ftrias/vindormusic/apps/juce-gui/Knob/JKnobMan/Resource/Images/JKnobMan.png

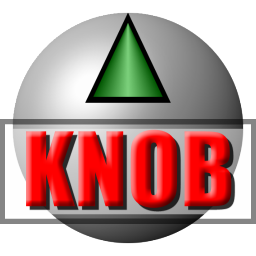
apps/juce-gui/Knob/JKnobMan/Resource/Images/JKnobMan.png
