ftrias/vindormusic/apps/juce-gui/Knob/JKnobMan/Texture/Plasma.bmp

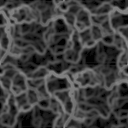
apps/juce-gui/Knob/JKnobMan/Texture/Plasma.bmp
