ftrias/vindormusic/apps/juce-gui/Assets/refresh.png

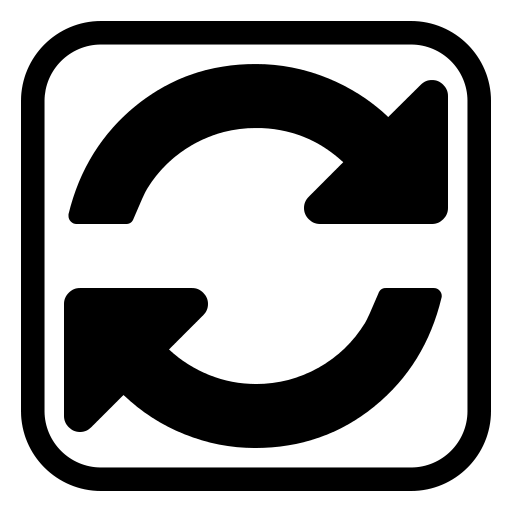
apps/juce-gui/Assets/refresh.png
