ftrias/vindormusic/apps/juce-gui/Assets/waveforms.png

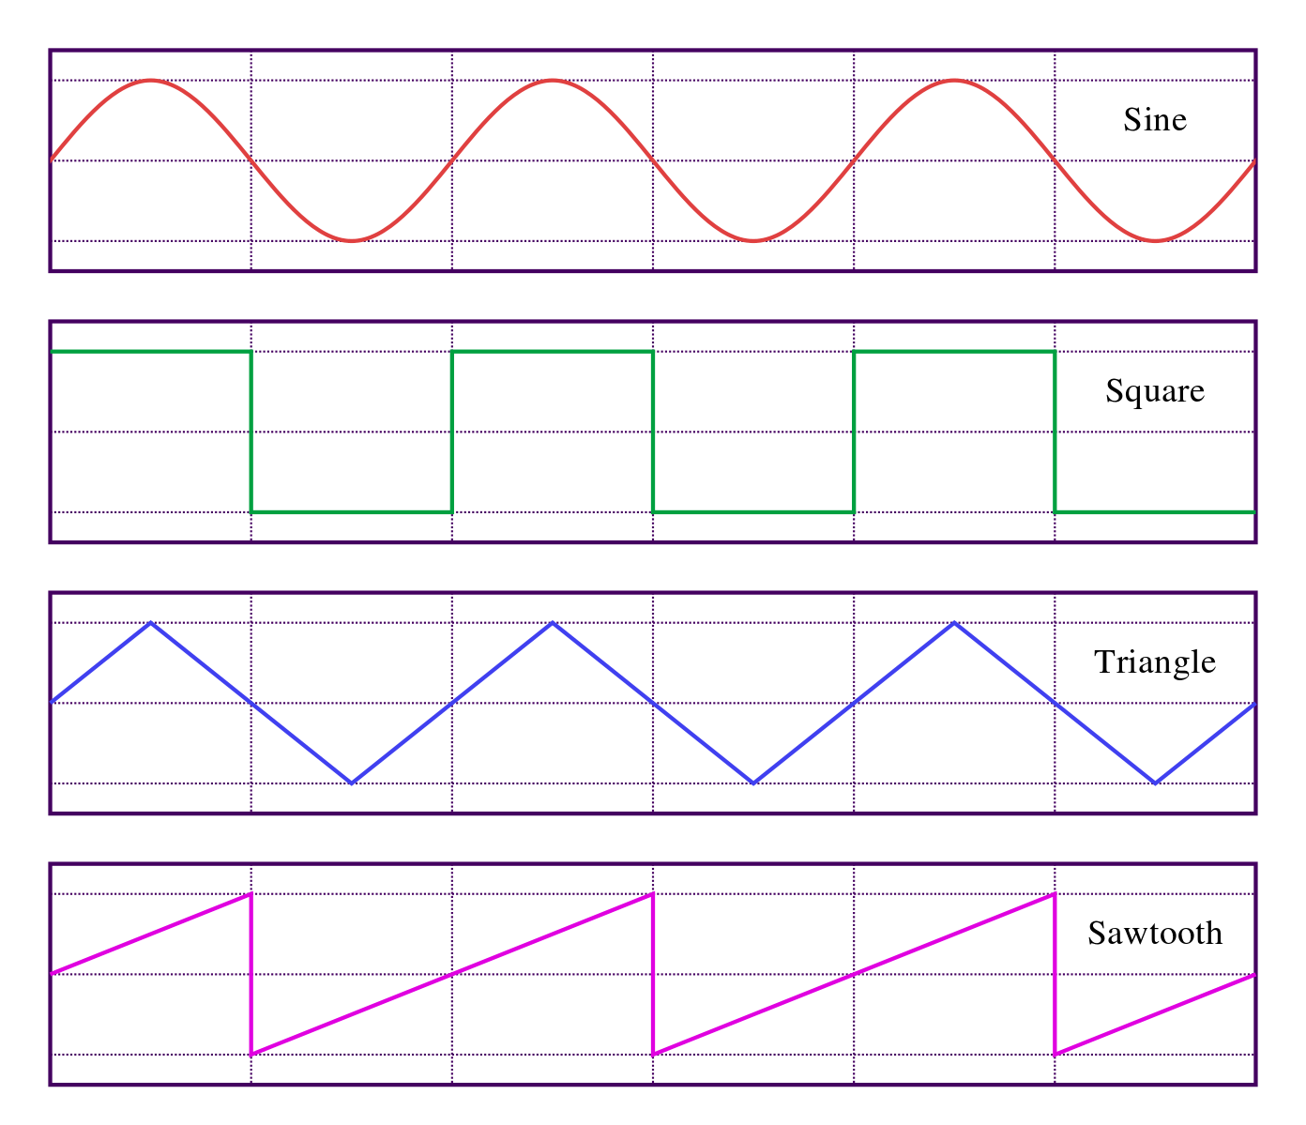
apps/juce-gui/Assets/waveforms.png
