ftrias/vindormusic/apps/juce-gui/Dist/Vindor WAP/Vindor WAP/Assets/LargeTile.scale-100.png

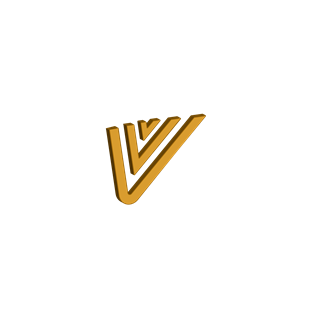
apps/juce-gui/Dist/Vindor WAP/Vindor WAP/Assets/LargeTile.scale-100.png
