ftrias/vindormusic/apps/juce-gui/Dist/Vindor WAP/Vindor WAP/Assets/SmallTile.scale-200.png

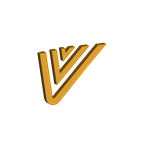
apps/juce-gui/Dist/Vindor WAP/Vindor WAP/Assets/SmallTile.scale-200.png
