ftrias/vindormusic/apps/juce-gui/Knob/JKnobMan/Resource/Images/pickercursor.png

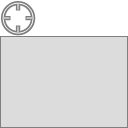
apps/juce-gui/Knob/JKnobMan/Resource/Images/pickercursor.png
