ftrias/vindormusic/apps/juce-gui/Knob/JKnobMan/Texture/Aura.jpg

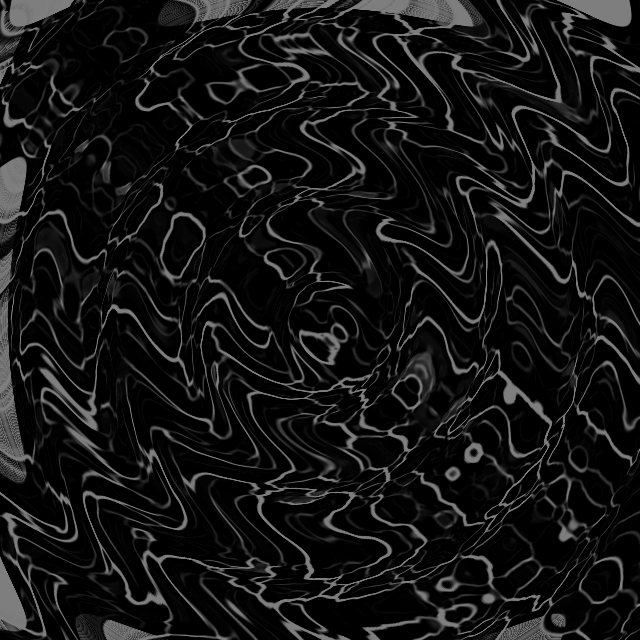
apps/juce-gui/Knob/JKnobMan/Texture/Aura.jpg
