ftrias/vindormusic/apps/juce-gui/Knob/JKnobMan/Texture/Circle.jpg

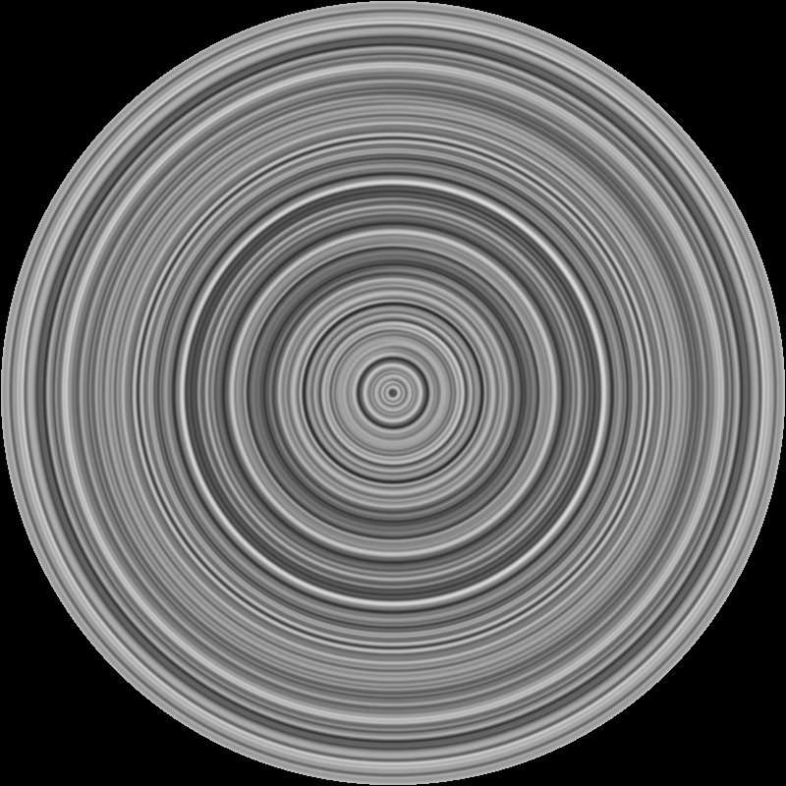
apps/juce-gui/Knob/JKnobMan/Texture/Circle.jpg
