ftrias/vindormusic/apps/juce-gui/Knob/JKnobMan/Texture/Coal.jpg

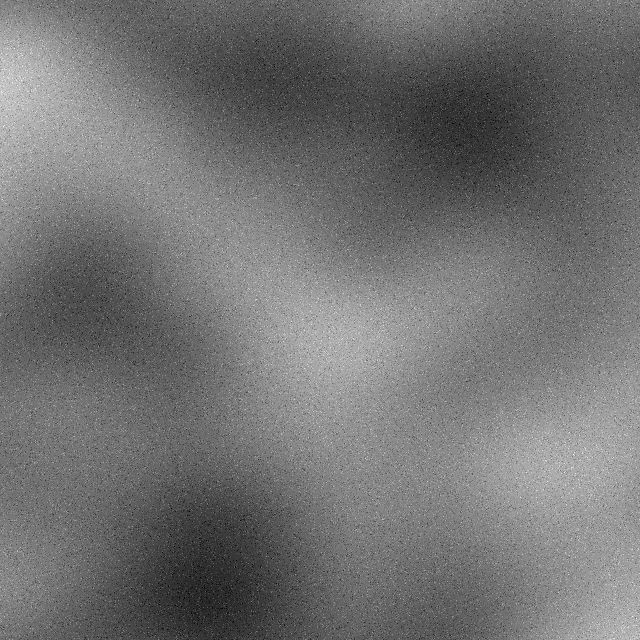
apps/juce-gui/Knob/JKnobMan/Texture/Coal.jpg
