ftrias/vindormusic/apps/juce-gui/Knob/JKnobMan/Texture/Fabric.bmp

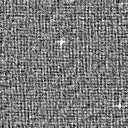
apps/juce-gui/Knob/JKnobMan/Texture/Fabric.bmp
