ftrias/vindormusic/apps/juce-gui/Knob/JKnobMan/Texture/Hairline.bmp

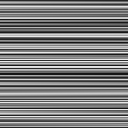
apps/juce-gui/Knob/JKnobMan/Texture/Hairline.bmp
