ftrias/vindormusic/apps/juce-gui/Knob/JKnobMan/Texture/HairlineV.bmp

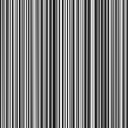
apps/juce-gui/Knob/JKnobMan/Texture/HairlineV.bmp
