ftrias/vindormusic/apps/juce-gui/Knob/JKnobMan/Texture/Magma.bmp

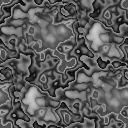
apps/juce-gui/Knob/JKnobMan/Texture/Magma.bmp
