ftrias/vindormusic/apps/juce-gui/Knob/JKnobMan/Texture/Mosaic.bmp

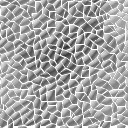
apps/juce-gui/Knob/JKnobMan/Texture/Mosaic.bmp
