ftrias/vindormusic/apps/juce-gui/Knob/JKnobMan/Texture/Plant.png

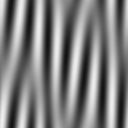
apps/juce-gui/Knob/JKnobMan/Texture/Plant.png
