ftrias/vindormusic/apps/juce-gui/Knob/JKnobMan/Texture/Radiation.jpg

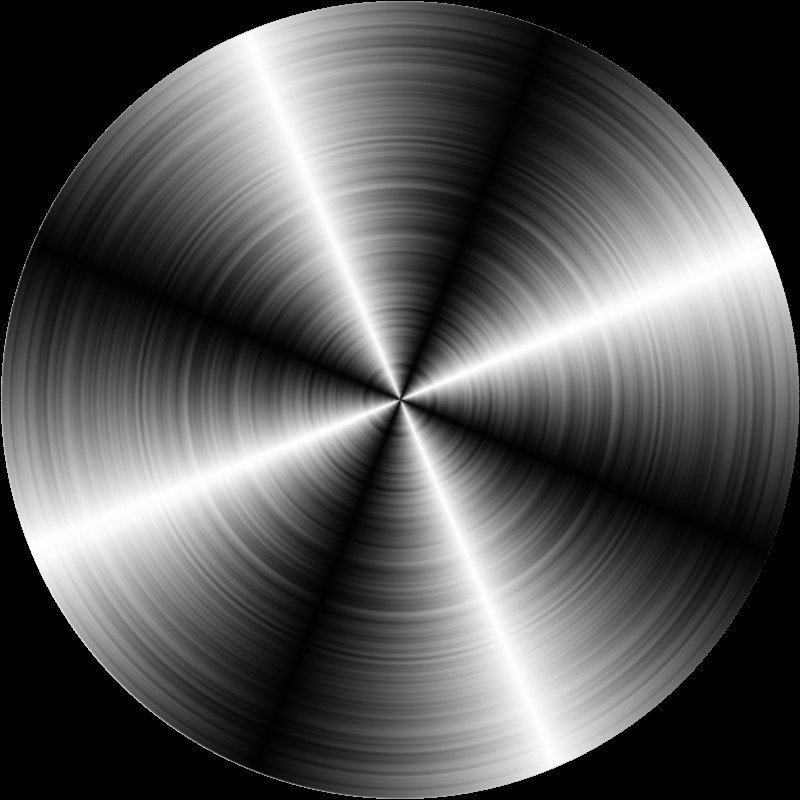
apps/juce-gui/Knob/JKnobMan/Texture/Radiation.jpg
