ftrias/vindormusic/apps/juce-gui/Knob/JKnobMan/Texture/Sand.bmp

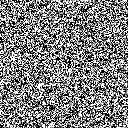
apps/juce-gui/Knob/JKnobMan/Texture/Sand.bmp
