ftrias/vindormusic/apps/juce-gui/Knob/JKnobMan/Texture/Scratch.jpg

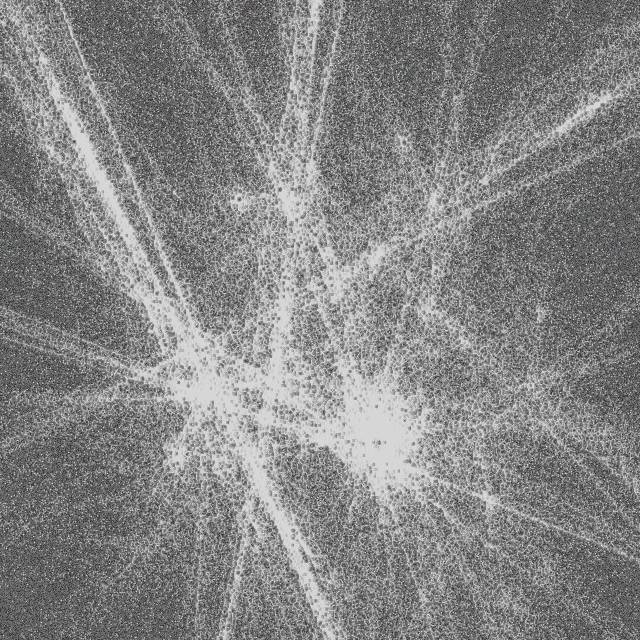
apps/juce-gui/Knob/JKnobMan/Texture/Scratch.jpg
