ftrias/vindormusic/apps/splayer/splayer/Source/Vindor.png

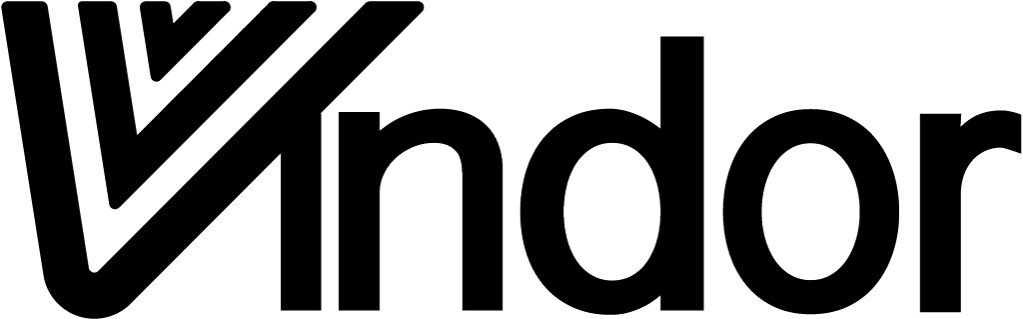
apps/splayer/splayer/Source/Vindor.png
