ftrias/vindormusic/shell/case/girl-playing.png

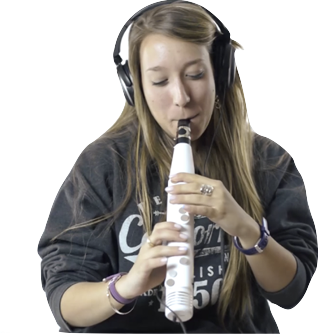
shell/case/girl-playing.png
