ftrias/vindormusic/shell/solidworks/Vindor RevD/2-56 screw 3_4in long 92196A084.SLDPRT

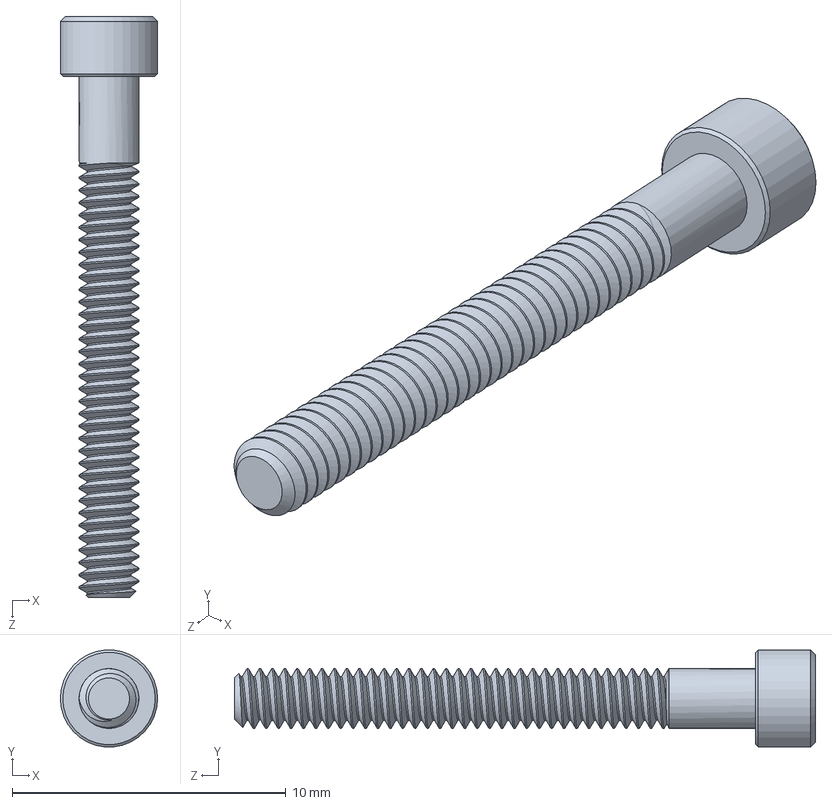
[picture p98: CAD file, 2024-02-22]
shell/solidworks/Vindor RevD/2-56 screw 3_4in long 92196A084.SLDPRT
3.56 x 3.54 x 21.2 mm
