ftrias/vindormusic/shell/solidworks/Vindor RevD/4-40 screw 7_16inlong 91772A109.SLDPRT

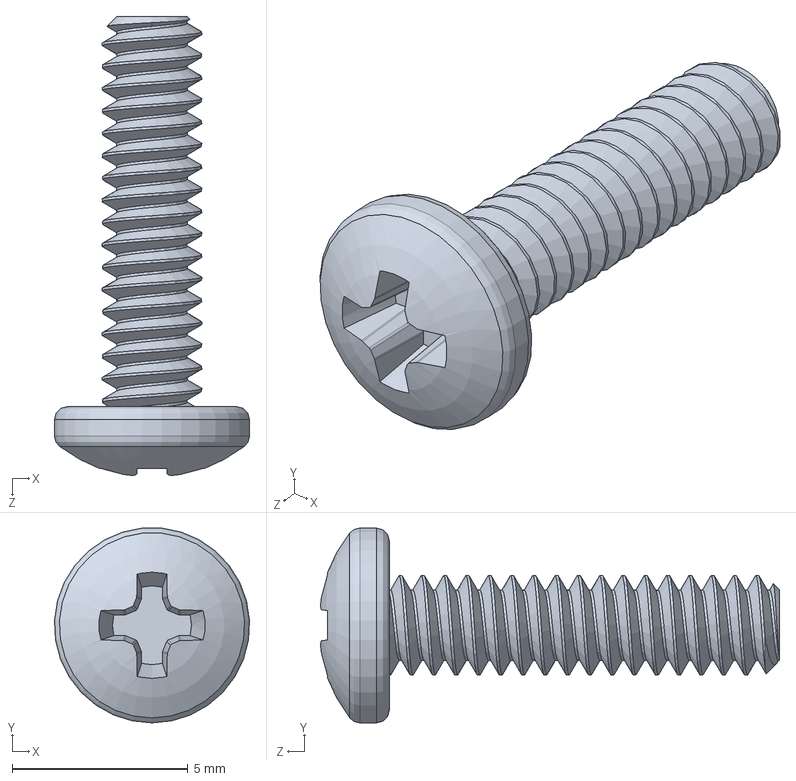
[picture p99: CAD file, 2024-02-22]
shell/solidworks/Vindor RevD/4-40 screw 7_16inlong 91772A109.SLDPRT
5.56 x 5.55 x 13.1 mm
