ftrias/vindormusic/shell/solidworks/Vindor RevD/4-40 Thread lock screw 1_4inlong 93802A421.SLDPRT

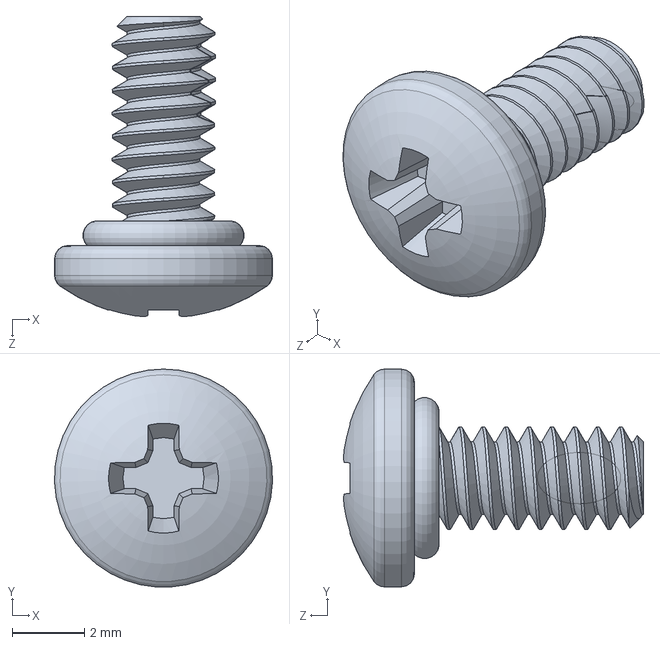
[picture p100: CAD file, 2024-02-22]
shell/solidworks/Vindor RevD/4-40 Thread lock screw 1_4inlong 93802A421.SLDPRT
6.04 x 6.04 x 8.32 mm
