ftrias/vindormusic/firmware/source/devices/pressuremap.h

const int expPressureBits = 10;
const int expPressureMap[1025] = {
0,0,3,5,9,13,17,22,27,33,39,46,53,60,68,76,84,93,101,111,
120,130,140,150,161,172,183,195,206,218,230,243,255,268,282,295,309,322,337,351,
365,380,395,410,426,441,457,473,489,506,522,539,556,573,591,608,626,644,662,681,
699,718,737,756,776,795,815,835,855,875,895,916,936,957,978,1000,1021,1043,1064,1086,
1109,1131,1153,1176,1199,1221,1245,1268,1291,1315,1339,1362,1386,1411,1435,1459,1484,1509,1534,1559,
1584,1610,1635,1661,1687,1713,1739,1766,1792,1819,1845,1872,1899,1927,1954,1982,2009,2037,2065,2093,
2121,2150,2178,2207,2235,2264,2293,2323,2352,2381,2411,2441,2471,2501,2531,2561,2592,2622,2653,2684,
2715,2746,2777,2808,2840,2871,2903,2935,2967,2999,3032,3064,3097,3129,3162,3195,3228,3261,3294,3328,
3361,3395,3429,3463,3497,3531,3565,3600,3634,3669,3704,3739,3774,3809,3844,3880,3915,3951,3987,4023,
4059,4095,4131,4167,4204,4240,4277,4314,4351,4388,4425,4463,4500,4538,4575,4613,4651,4689,4727,4766,
4804,4842,4881,4920,4959,4998,5037,5076,5115,5154,5194,5234,5273,5313,5353,5393,5433,5474,5514,5555,
5595,5636,5677,5718,5759,5800,5842,5883,5925,5966,6008,6050,6092,6134,6176,6218,6261,6303,6346,6388,
6431,6474,6517,6560,6604,6647,6690,6734,6778,6822,6865,6909,6953,6998,7042,7086,7131,7176,7220,7265,
7310,7355,7400,7445,7491,7536,7582,7628,7673,7719,7765,7811,7857,7904,7950,7996,8043,8090,8137,8183,
8230,8277,8325,8372,8419,8467,8514,8562,8610,8658,8706,8754,8802,8850,8899,8947,8996,9044,9093,9142,
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
40671,40757,40843,40929,41015,41100,41186,41272,41359,41445,41531,41617,41704,41790,41877,41963,42050,42137,42224,42311,
42397,42484,42572,42659,42746,42833,42920,43008,43095,43183,43270,43358,43446,43534,43622,43709,43798,43886,43974,44062,
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
