ftrias/vindormusic/firmware/source/sound/data_waveforms.c

#ifndef ARDUINO

/* Audio Library for Teensy 3.X
 * Copyright (c) 2014, Paul Stoffregen, paul@pjrc.com
 *
 * Development of this audio library was funded by PJRC.COM, LLC by sales of
 * Teensy and Audio Adaptor boards.  Please support PJRC's efforts to develop
 * open source software by purchasing Teensy or other PJRC products.
 *
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
 * THE SOFTWARE IS PROVIDED "AS IS", WITHOUT WARRANTY OF ANY KIND, EXPRESS OR
 * IMPLIED, INCLUDING BUT NOT LIMITED TO THE WARRANTIES OF MERCHANTABILITY,
 * FITNESS FOR A PARTICULAR PURPOSE AND NONINFRINGEMENT. IN NO EVENT SHALL THE
 * AUTHORS OR COPYRIGHT HOLDERS BE LIABLE FOR ANY CLAIM, DAMAGES OR OTHER
 * LIABILITY, WHETHER IN AN ACTION OF CONTRACT, TORT OR OTHERWISE, ARISING FROM,
 * OUT OF OR IN CONNECTION WITH THE SOFTWARE OR THE USE OR OTHER DEALINGS IN
 * THE SOFTWARE.
 */

#include <stdint.h>

// These audio waveforms have a period of 256 points, plus a 257th
// point that is a duplicate of the first point.  This duplicate
// is needed because the waveform generator uses linear interpolation
// between each point and the next point in the waveform.

const int16_t AudioWaveformSine[257] = {
     0,   804,  1608,  2410,  3212,  4011,  4808,  5602,  6393,  7179,
  7962,  8739,  9512, 10278, 11039, 11793, 12539, 13279, 14010, 14732,
 15446, 16151, 16846, 17530, 18204, 18868, 19519, 20159, 20787, 21403,
 22005, 22594, 23170, 23731, 24279, 24811, 25329, 25832, 26319, 26790,
 27245, 27683, 28105, 28510, 28898, 29268, 29621, 29956, 30273, 30571,
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
for ($i=0; $i < $len+1; $i++) {
        $a = cos(3.14149 * $i / $len);
        $in = (1 - $a) / 2;
        $d = $in * 32768;
        $d = 32767 if $d >= 32767.5;
        printf "%5d", $d;
        print "," if ($i < $len);
        print "\n" if ($i % 10) == 9;
}
print "\n};\n";
#endif

#endif
