ftrias/vindormusic/firmware/source/Constants.h

#ifndef CONSTANTS_H
#define CONSTANTS_H

/* Using code for Hartmann GmbH, an expired manufacturer
 * see http://www.midi.org/techspecs/manid.php
 */
const unsigned char MIDI_MFG1=0x00;
const unsigned char MIDI_MFG2=0x20;
const unsigned char MIDI_MFG3=0x50;

#endif
