ftrias/vindormusic/firmware/source/devices/SdLib.cpp

/**
 * @file SdLib.cpp
 * @author Fernando Trias
 * @brief Emulate SD behavior using SdFs library
 * @version 0.1
 * @date 2020
 * 
 * @copyright Copyright (c) 2020 by Vindor Music, Inc.
 * 
 */

#include <Arduino.h>
#include <SdFat.h>
SdFat SD;
