ftrias/vindormusic/apps/juce-gui/Source/DFU/dfu.c

/*
 * Low-level DFU communication routines, originally taken from
 * $Id: dfu.c,v 1.3 2006/06/20 06:28:04 schmidtw Exp $
 * (part of dfu-programmer).
 *
 * Copyright 2005-2006 Weston Schmidt <weston_schmidt@alumni.purdue.edu>
 * Copyright 2011-2014 Tormod Volden <debian.tormod@gmail.com>
 *
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
 * You should have received a copy of the GNU General Public License
 * along with this program; if not, write to the Free Software
 * Foundation, Inc., 59 Temple Place, Suite 330, Boston, MA  02111-1307  USA
 */

#include <stdio.h>
#include <stdlib.h>

#include <libusb.h>

#include "portable.h"
#include "dfu.h"
#include "quirks.h"

static int dfu_timeout = 5000;  /* 5 seconds - default */

/*
 *  DFU_DETACH Request (DFU Spec 1.0, Section 5.1)
 *
 *  device    - the usb_dev_handle to communicate with
 *  interface - the interface to communicate with
 *  timeout   - the timeout in ms the USB device should wait for a pending
 *              USB reset before giving up and terminating the operation
 *
 *  returns 0 or < 0 on error
 */
int dfu_detach( libusb_device_handle *device,
                const unsigned short interface,
                const unsigned short timeout )
{
    return libusb_control_transfer( device,
        /* bmRequestType */ LIBUSB_ENDPOINT_OUT | LIBUSB_REQUEST_TYPE_CLASS | LIBUSB_RECIPIENT_INTERFACE,
        /* bRequest      */ DFU_DETACH,
        /* wValue        */ timeout,
        /* wIndex        */ interface,
        /* Data          */ NULL,
        /* wLength       */ 0,
                            dfu_timeout );
}


/*
 *  DFU_DNLOAD Request (DFU Spec 1.0, Section 6.1.1)
 *
 *  device    - the usb_dev_handle to communicate with
 *  interface - the interface to communicate with
 *  length    - the total number of bytes to transfer to the USB
 *              device - must be less than wTransferSize
 *  data      - the data to transfer
 *
 *  returns the number of bytes written or < 0 on error
 */
int dfu_download( libusb_device_handle *device,
                  const unsigned short interface,
                  const unsigned short length,
                  const unsigned short transaction,
                  unsigned char* data )
{
    int status;

    status = libusb_control_transfer( device,
          /* bmRequestType */ LIBUSB_ENDPOINT_OUT | LIBUSB_REQUEST_TYPE_CLASS | LIBUSB_RECIPIENT_INTERFACE,
          /* bRequest      */ DFU_DNLOAD,
          /* wValue        */ transaction,
          /* wIndex        */ interface,
          /* Data          */ data,
          /* wLength       */ length,
                              dfu_timeout );
    return status;
}


/*
 *  DFU_UPLOAD Request (DFU Spec 1.0, Section 6.2)
 *
 *  device    - the usb_dev_handle to communicate with
 *  interface - the interface to communicate with
 *  length    - the maximum number of bytes to receive from the USB
 *              device - must be less than wTransferSize
 *  data      - the buffer to put the received data in
 *
 *  returns the number of bytes received or < 0 on error
 */
int dfu_upload( libusb_device_handle *device,
                const unsigned short interface,
                const unsigned short length,
                const unsigned short transaction,
                unsigned char* data )
{
    int status;

    status = libusb_control_transfer( device,
          /* bmRequestType */ LIBUSB_ENDPOINT_IN | LIBUSB_REQUEST_TYPE_CLASS | LIBUSB_RECIPIENT_INTERFACE,
          /* bRequest      */ DFU_UPLOAD,
          /* wValue        */ transaction,
          /* wIndex        */ interface,
          /* Data          */ data,
          /* wLength       */ length,
                              dfu_timeout );
    return status;
}


/*
 *  DFU_GETSTATUS Request (DFU Spec 1.0, Section 6.1.2)
 *
 *  device    - the usb_dev_handle to communicate with
 *  interface - the interface to communicate with
 *  status    - the data structure to be populated with the results
 *
 *  return the number of bytes read in or < 0 on an error
 */
int dfu_get_status( struct dfu_if *dif, struct dfu_status *status )
{
    unsigned char buffer[6];
    int result;

    /* Initialize the status data structure */
    status->bStatus       = DFU_STATUS_ERROR_UNKNOWN;
    status->bwPollTimeout = 0;
    status->bState        = STATE_DFU_ERROR;
    status->iString       = 0;

    result = libusb_control_transfer( dif->dev_handle,
          /* bmRequestType */ LIBUSB_ENDPOINT_IN | LIBUSB_REQUEST_TYPE_CLASS | LIBUSB_RECIPIENT_INTERFACE,
          /* bRequest      */ DFU_GETSTATUS,
          /* wValue        */ 0,
          /* wIndex        */ dif->interface,
          /* Data          */ buffer,
          /* wLength       */ 6,
                              dfu_timeout );

    if( 6 == result ) {
        status->bStatus = buffer[0];
        if (dif->quirks & QUIRK_POLLTIMEOUT)
            status->bwPollTimeout = DEFAULT_POLLTIMEOUT;
        else
            status->bwPollTimeout = ((0xff & buffer[3]) << 16) |
                                    ((0xff & buffer[2]) << 8)  |
                                    (0xff & buffer[1]);
        status->bState  = buffer[4];
        status->iString = buffer[5];
    }

    return result;
}


/*
 *  DFU_CLRSTATUS Request (DFU Spec 1.0, Section 6.1.3)
 *
 *  device    - the usb_dev_handle to communicate with
 *  interface - the interface to communicate with
 *
 *  return 0 or < 0 on an error
 */
int dfu_clear_status( libusb_device_handle *device,
                      const unsigned short interface )
{
    return libusb_control_transfer( device,
        /* bmRequestType */ LIBUSB_ENDPOINT_OUT| LIBUSB_REQUEST_TYPE_CLASS | LIBUSB_RECIPIENT_INTERFACE,
        /* bRequest      */ DFU_CLRSTATUS,
        /* wValue        */ 0,
        /* wIndex        */ interface,
        /* Data          */ NULL,
        /* wLength       */ 0,
                            dfu_timeout );
}


/*
 *  DFU_GETSTATE Request (DFU Spec 1.0, Section 6.1.5)
 *
 *  device    - the usb_dev_handle to communicate with
 *  interface - the interface to communicate with
 *  length    - the maximum number of bytes to receive from the USB
 *              device - must be less than wTransferSize
 *  data      - the buffer to put the received data in
 *
 *  returns the state or < 0 on error
 */
int dfu_get_state( libusb_device_handle *device,
                   const unsigned short interface )
{
    int result;
    unsigned char buffer[1];

    result = libusb_control_transfer( device,
          /* bmRequestType */ LIBUSB_ENDPOINT_IN | LIBUSB_REQUEST_TYPE_CLASS | LIBUSB_RECIPIENT_INTERFACE,
          /* bRequest      */ DFU_GETSTATE,
          /* wValue        */ 0,
          /* wIndex        */ interface,
          /* Data          */ buffer,
          /* wLength       */ 1,
                              dfu_timeout );

    /* Return the error if there is one. */
    if (result < 1)
	return -1;

    /* Return the state. */
    return buffer[0];
}


/*
 *  DFU_ABORT Request (DFU Spec 1.0, Section 6.1.4)
 *
 *  device    - the usb_dev_handle to communicate with
 *  interface - the interface to communicate with
 *
 *  returns 0 or < 0 on an error
 */
int dfu_abort( libusb_device_handle *device,
               const unsigned short interface )
{
    return libusb_control_transfer( device,
        /* bmRequestType */ LIBUSB_ENDPOINT_OUT | LIBUSB_REQUEST_TYPE_CLASS | LIBUSB_RECIPIENT_INTERFACE,
        /* bRequest      */ DFU_ABORT,
        /* wValue        */ 0,
        /* wIndex        */ interface,
        /* Data          */ NULL,
        /* wLength       */ 0,
                            dfu_timeout );
}


const char* dfu_state_to_string( int state )
{
    const char *message;

    switch (state) {
        case STATE_APP_IDLE:
            message = "appIDLE";
            break;
        case STATE_APP_DETACH:
            message = "appDETACH";
            break;
        case STATE_DFU_IDLE:
            message = "dfuIDLE";
            break;
        case STATE_DFU_DOWNLOAD_SYNC:
            message = "dfuDNLOAD-SYNC";
            break;
        case STATE_DFU_DOWNLOAD_BUSY:
            message = "dfuDNBUSY";
            break;
        case STATE_DFU_DOWNLOAD_IDLE:
            message = "dfuDNLOAD-IDLE";
            break;
        case STATE_DFU_MANIFEST_SYNC:
            message = "dfuMANIFEST-SYNC";
            break;
        case STATE_DFU_MANIFEST:
            message = "dfuMANIFEST";
            break;
        case STATE_DFU_MANIFEST_WAIT_RESET:
            message = "dfuMANIFEST-WAIT-RESET";
            break;
        case STATE_DFU_UPLOAD_IDLE:
            message = "dfuUPLOAD-IDLE";
            break;
        case STATE_DFU_ERROR:
            message = "dfuERROR";
            break;
        default:
            message = NULL;
            break;
    }

    return message;
}

/* Chapter 6.1.2 */
static const char *dfu_status_names[] = {
	/* DFU_STATUS_OK */
		"No error condition is present",
	/* DFU_STATUS_errTARGET */
		"File is not targeted for use by this device",
	/* DFU_STATUS_errFILE */
		"File is for this device but fails some vendor-specific test",
	/* DFU_STATUS_errWRITE */
		"Device is unable to write memory",
	/* DFU_STATUS_errERASE */
		"Memory erase function failed",
	/* DFU_STATUS_errCHECK_ERASED */
		"Memory erase check failed",
	/* DFU_STATUS_errPROG */
		"Program memory function failed",
	/* DFU_STATUS_errVERIFY */
		"Programmed memory failed verification",
	/* DFU_STATUS_errADDRESS */
		"Cannot program memory due to received address that is out of range",
	/* DFU_STATUS_errNOTDONE */
		"Received DFU_DNLOAD with wLength = 0, but device does not think that it has all data yet",
	/* DFU_STATUS_errFIRMWARE */
		"Device's firmware is corrupt. It cannot return to run-time (non-DFU) operations",
	/* DFU_STATUS_errVENDOR */
		"iString indicates a vendor specific error",
	/* DFU_STATUS_errUSBR */
		"Device detected unexpected USB reset signalling",
	/* DFU_STATUS_errPOR */
		"Device detected unexpected power on reset",
	/* DFU_STATUS_errUNKNOWN */
		"Something went wrong, but the device does not know what it was",
	/* DFU_STATUS_errSTALLEDPKT */
		"Device stalled an unexpected request"
};


const char *dfu_status_to_string(int status)
{
	if (status > DFU_STATUS_errSTALLEDPKT)
		return "INVALID";
	return dfu_status_names[status];
}

int dfu_abort_to_idle(struct dfu_if *dif)
{
	int ret;
	struct dfu_status dst;

	ret = dfu_abort(dif->dev_handle, dif->interface);
	if (ret < 0) {
		errxx(EX_IOERR, "Error sending dfu abort request");
		return(1);
	}
	ret = dfu_get_status(dif, &dst);
	if (ret < 0) {
		errxx(EX_IOERR, "Error during abort get_status");
		return(1);
	}
	if (dst.bState != DFU_STATE_dfuIDLE) {
		errxx(EX_IOERR, "Failed to enter idle state on abort");
		return(1);
	}
	milli_sleep(dst.bwPollTimeout);
	return ret;
}
