ftrias/vindormusic/firmware/dfu/bootloader/kinetis.h

/* Teensyduino Core Library
 * http://www.pjrc.com/teensy/
 * Copyright (c) 2013 PJRC.COM, LLC.
 *
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
 * 2. If the Software is incorporated into a build system that allows
 * selection among a list of target devices, then similar target
 * devices manufactured by PJRC.COM must be included in the list of
 * target devices and selectable in the same manner.
 *
 * THE SOFTWARE IS PROVIDED "AS IS", WITHOUT WARRANTY OF ANY KIND,
 * EXPRESS OR IMPLIED, INCLUDING BUT NOT LIMITED TO THE WARRANTIES OF
 * MERCHANTABILITY, FITNESS FOR A PARTICULAR PURPOSE AND
 * NONINFRINGEMENT. IN NO EVENT SHALL THE AUTHORS OR COPYRIGHT HOLDERS
 * BE LIABLE FOR ANY CLAIM, DAMAGES OR OTHER LIABILITY, WHETHER IN AN
 * ACTION OF CONTRACT, TORT OR OTHERWISE, ARISING FROM, OUT OF OR IN
 * CONNECTION WITH THE SOFTWARE OR THE USE OR OTHER DEALINGS IN THE
 * SOFTWARE.
 */

#ifndef _kinetis_h_
#define _kinetis_h_

#include <stdint.h>

// Teensy 3.0
#if defined(__MK20DX128__)
enum IRQ_NUMBER_t {
	IRQ_DMA_CH0 =		0,
	IRQ_DMA_CH1 =		1,
	IRQ_DMA_CH2 =		2,
	IRQ_DMA_CH3 =		3,
	IRQ_DMA_ERROR =		4,
	IRQ_FTFL_COMPLETE =	6,
	IRQ_FTFL_COLLISION =	7,
	IRQ_LOW_VOLTAGE =	8,
	IRQ_LLWU =		9,
	IRQ_WDOG =		10,
	IRQ_I2C0 =		11,
	IRQ_SPI0 =		12,
	IRQ_I2S0_TX =		13,
	IRQ_I2S0_RX =		14,
	IRQ_UART0_LON =		15,
	IRQ_UART0_STATUS =	16,
	IRQ_UART0_ERROR =	17,
	IRQ_UART1_STATUS =	18,
	IRQ_UART1_ERROR =	19,
	IRQ_UART2_STATUS =	20,
	IRQ_UART2_ERROR =	21,
	IRQ_ADC0 =		22,
	IRQ_CMP0 =		23,
	IRQ_CMP1 =		24,
	IRQ_FTM0 =		25,
	IRQ_FTM1 =		26,
	IRQ_CMT =		27,
	IRQ_RTC_ALARM =		28,
	IRQ_RTC_SECOND =	29,
	IRQ_PIT_CH0 =		30,
	IRQ_PIT_CH1 =		31,
	IRQ_PIT_CH2 =		32,
	IRQ_PIT_CH3 =		33,
	IRQ_PDB =		34,
	IRQ_USBOTG =		35,
	IRQ_USBDCD =		36,
	IRQ_TSI =		37,
	IRQ_MCG =		38,
	IRQ_LPTMR =		39,
	IRQ_PORTA =		40,
	IRQ_PORTB =		41,
	IRQ_PORTC =		42,
	IRQ_PORTD =		43,
	IRQ_PORTE =		44,
	IRQ_SOFTWARE =		45
};
#define NVIC_NUM_INTERRUPTS	46
#define DMA_NUM_CHANNELS	4
#define KINETISK
#define HAS_KINETISK_UART0
#define HAS_KINETISK_UART0_FIFO
#define HAS_KINETISK_UART1
#define HAS_KINETISK_UART2
#define HAS_KINETIS_I2C0

// Teensy 3.1
#elif defined(__MK20DX256__)
enum IRQ_NUMBER_t {
	IRQ_DMA_CH0 =		0,
	IRQ_DMA_CH1 =		1,
	IRQ_DMA_CH2 =		2,
	IRQ_DMA_CH3 =		3,
	IRQ_DMA_CH4 =		4,
	IRQ_DMA_CH5 =		5,
	IRQ_DMA_CH6 =		6,
	IRQ_DMA_CH7 =		7,
	IRQ_DMA_CH8 =		8,
	IRQ_DMA_CH9 =		9,
	IRQ_DMA_CH10 =		10,
	IRQ_DMA_CH11 =		11,
	IRQ_DMA_CH12 =		12,
	IRQ_DMA_CH13 =		13,
	IRQ_DMA_CH14 =		14,
	IRQ_DMA_CH15 =		15,
	IRQ_DMA_ERROR =		16,
	IRQ_FTFL_COMPLETE =	18,
	IRQ_FTFL_COLLISION =	19,
	IRQ_LOW_VOLTAGE =	20,
	IRQ_LLWU =		21,
	IRQ_WDOG =		22,
	IRQ_I2C0 =		24,
	IRQ_I2C1 =		25,
	IRQ_SPI0 =		26,
	IRQ_SPI1 =		27,
	IRQ_CAN_MESSAGE =	29,
	IRQ_CAN_BUS_OFF =	30,
	IRQ_CAN_ERROR =		31,
	IRQ_CAN_TX_WARN =	32,
	IRQ_CAN_RX_WARN =	33,
	IRQ_CAN_WAKEUP =	34,
	IRQ_I2S0_TX =		35,
	IRQ_I2S0_RX =		36,
	IRQ_UART0_LON =		44,
	IRQ_UART0_STATUS =	45,
	IRQ_UART0_ERROR =	46,
	IRQ_UART1_STATUS =	47,
	IRQ_UART1_ERROR =	48,
	IRQ_UART2_STATUS =	49,
	IRQ_UART2_ERROR =	50,
	IRQ_ADC0 =		57,
	IRQ_ADC1 =		58,
	IRQ_CMP0 =		59,
	IRQ_CMP1 =		60,
	IRQ_CMP2 =		61,
	IRQ_FTM0 =		62,
	IRQ_FTM1 =		63,
	IRQ_FTM2 =		64,
	IRQ_CMT =		65,
	IRQ_RTC_ALARM =		66,
	IRQ_RTC_SECOND =	67,
	IRQ_PIT_CH0 =		68,
	IRQ_PIT_CH1 =		69,
	IRQ_PIT_CH2 =		70,
	IRQ_PIT_CH3 =		71,
	IRQ_PDB =		72,
	IRQ_USBOTG =		73,
	IRQ_USBDCD =		74,
	IRQ_DAC0 =		81,
	IRQ_TSI =		83,
	IRQ_MCG =		84,
	IRQ_LPTMR =		85,
	IRQ_PORTA =		87,
	IRQ_PORTB =		88,
	IRQ_PORTC =		89,
	IRQ_PORTD =		90,
	IRQ_PORTE =		91,
	IRQ_SOFTWARE =		94
};
#define NVIC_NUM_INTERRUPTS	95
#define DMA_NUM_CHANNELS	16
#define KINETISK
#define HAS_KINETISK_UART0
#define HAS_KINETISK_UART0_FIFO
#define HAS_KINETISK_UART1
#define HAS_KINETISK_UART1_FIFO
#define HAS_KINETISK_UART2
#define HAS_KINETIS_I2C0
#define HAS_KINETIS_I2C1

#elif defined(__MKL26Z64__)
enum IRQ_NUMBER_t {
	IRQ_DMA_CH0 =		0,
	IRQ_DMA_CH1 =		1,
	IRQ_DMA_CH2 =		2,
	IRQ_DMA_CH3 =		3,
        IRQ_FTFA =              5,
        IRQ_LOW_VOLTAGE =       6,
        IRQ_LLWU =              7,
        IRQ_I2C0 =              8,
        IRQ_I2C1 =              9,
        IRQ_SPI0 =              10,
        IRQ_SPI1 =              11,
        IRQ_UART0_STATUS =      12,
        IRQ_UART1_STATUS =      13,
        IRQ_UART2_STATUS =      14,
        IRQ_ADC0 =              15,
        IRQ_CMP0 =              16,
        IRQ_FTM0 =              17,
        IRQ_FTM1 =              18,
        IRQ_FTM2 =              19,
        IRQ_RTC_ALARM =         20,
        IRQ_RTC_SECOND =        21,
        IRQ_PIT =               22,
        IRQ_I2S0 =              23,
        IRQ_USBOTG =            24,
        IRQ_DAC0 =              25,
        IRQ_TSI =               26,
        IRQ_MCG =               27,
        IRQ_LPTMR =             28,
	IRQ_SOFTWARE =		29,  // TODO: verify this works
        IRQ_PORTA =             30,
        IRQ_PORTCD =            31
};
#define NVIC_NUM_INTERRUPTS     32
#define DMA_NUM_CHANNELS        4
#define KINETISL
#define HAS_KINETISL_UART0
#define HAS_KINETISL_UART1
#define HAS_KINETISL_UART2
#define HAS_KINETIS_I2C0
#define HAS_KINETIS_I2C0_STOPF
#define HAS_KINETIS_I2C1
#define HAS_KINETIS_I2C1_STOPF

#endif // end of board-specific definitions


#if (F_CPU == 168000000)
 #define F_PLL 168000000
 #define F_BUS 56000000
 #define F_MEM 33600000
#elif (F_CPU == 144000000)
 #define F_PLL 144000000
 #define F_BUS 48000000
 #define F_MEM 28800000
#elif (F_CPU == 120000000)
 #define F_PLL 120000000
 #define F_BUS 60000000
 #define F_MEM 24000000
#elif (F_CPU == 96000000)
 #define F_PLL 96000000
 #define F_BUS 48000000
 #define F_MEM 24000000
#elif (F_CPU == 72000000)
 #define F_PLL 72000000
 #define F_BUS 36000000
 #define F_MEM 24000000
#elif (F_CPU == 48000000)
 #define F_PLL 96000000
 #if defined(KINETISK)
 #define F_BUS 48000000
 #elif defined(KINETISL)
 #define F_BUS 24000000
 #endif
 #define F_MEM 24000000
#elif (F_CPU == 24000000)
 #define F_PLL 96000000
 #define F_BUS 24000000
 #define F_MEM 24000000
#elif (F_CPU == 16000000)
 #define F_PLL 16000000
 #define F_BUS 16000000
 #define F_MEM 16000000
#elif (F_CPU == 8000000)
 #define F_PLL 8000000
 #define F_BUS 8000000
 #define F_MEM 8000000
#elif (F_CPU == 4000000)
 #define F_PLL 4000000
 #define F_BUS 4000000
 #define F_MEM 4000000
#elif (F_CPU == 2000000)
 #define F_PLL 2000000
 #define F_BUS 2000000
 #define F_MEM 1000000
#endif


#ifndef NULL
#define NULL ((void *)0)
#endif

// chapter 11: Port control and interrupts (PORT)
#define PORTA_PCR0		(*(volatile uint32_t *)0x40049000) // Pin Control Register n
#define PORT_PCR_ISF			((uint32_t)0x01000000)		// Interrupt Status Flag
#define PORT_PCR_IRQC(n)		((uint32_t)(((n) & 15) << 16))	// Interrupt Configuration
#define PORT_PCR_IRQC_MASK		((uint32_t)0x000F0000)
#define PORT_PCR_LK			((uint32_t)0x00008000)		// Lock Register
#define PORT_PCR_MUX(n)			((uint32_t)(((n) & 7) << 8))	// Pin Mux Control
#define PORT_PCR_MUX_MASK		((uint32_t)0x00000700)
#define PORT_PCR_DSE			((uint32_t)0x00000040)		// Drive Strength Enable
#define PORT_PCR_ODE			((uint32_t)0x00000020)		// Open Drain Enable
#define PORT_PCR_PFE			((uint32_t)0x00000010)		// Passive Filter Enable
#define PORT_PCR_SRE			((uint32_t)0x00000004)		// Slew Rate Enable
#define PORT_PCR_PE			((uint32_t)0x00000002)		// Pull Enable
#define PORT_PCR_PS			((uint32_t)0x00000001)		// Pull Select
#define PORTA_PCR1		(*(volatile uint32_t *)0x40049004) // Pin Control Register n
#define PORTA_PCR2		(*(volatile uint32_t *)0x40049008) // Pin Control Register n
#define PORTA_PCR3		(*(volatile uint32_t *)0x4004900C) // Pin Control Register n
#define PORTA_PCR4		(*(volatile uint32_t *)0x40049010) // Pin Control Register n
#define PORTA_PCR5		(*(volatile uint32_t *)0x40049014) // Pin Control Register n
#define PORTA_PCR6		(*(volatile uint32_t *)0x40049018) // Pin Control Register n
#define PORTA_PCR7		(*(volatile uint32_t *)0x4004901C) // Pin Control Register n
#define PORTA_PCR8		(*(volatile uint32_t *)0x40049020) // Pin Control Register n
#define PORTA_PCR9		(*(volatile uint32_t *)0x40049024) // Pin Control Register n
#define PORTA_PCR10		(*(volatile uint32_t *)0x40049028) // Pin Control Register n
#define PORTA_PCR11		(*(volatile uint32_t *)0x4004902C) // Pin Control Register n
#define PORTA_PCR12		(*(volatile uint32_t *)0x40049030) // Pin Control Register n
#define PORTA_PCR13		(*(volatile uint32_t *)0x40049034) // Pin Control Register n
#define PORTA_PCR14		(*(volatile uint32_t *)0x40049038) // Pin Control Register n
#define PORTA_PCR15		(*(volatile uint32_t *)0x4004903C) // Pin Control Register n
#define PORTA_PCR16		(*(volatile uint32_t *)0x40049040) // Pin Control Register n
#define PORTA_PCR17		(*(volatile uint32_t *)0x40049044) // Pin Control Register n
#define PORTA_PCR18		(*(volatile uint32_t *)0x40049048) // Pin Control Register n
#define PORTA_PCR19		(*(volatile uint32_t *)0x4004904C) // Pin Control Register n
#define PORTA_PCR20		(*(volatile uint32_t *)0x40049050) // Pin Control Register n
#define PORTA_PCR21		(*(volatile uint32_t *)0x40049054) // Pin Control Register n
#define PORTA_PCR22		(*(volatile uint32_t *)0x40049058) // Pin Control Register n
#define PORTA_PCR23		(*(volatile uint32_t *)0x4004905C) // Pin Control Register n
#define PORTA_PCR24		(*(volatile uint32_t *)0x40049060) // Pin Control Register n
#define PORTA_PCR25		(*(volatile uint32_t *)0x40049064) // Pin Control Register n
#define PORTA_PCR26		(*(volatile uint32_t *)0x40049068) // Pin Control Register n
#define PORTA_PCR27		(*(volatile uint32_t *)0x4004906C) // Pin Control Register n
#define PORTA_PCR28		(*(volatile uint32_t *)0x40049070) // Pin Control Register n
#define PORTA_PCR29		(*(volatile uint32_t *)0x40049074) // Pin Control Register n
#define PORTA_PCR30		(*(volatile uint32_t *)0x40049078) // Pin Control Register n
#define PORTA_PCR31		(*(volatile uint32_t *)0x4004907C) // Pin Control Register n
#define PORTA_GPCLR		(*(volatile uint32_t *)0x40049080) // Global Pin Control Low Register
#define PORTA_GPCHR		(*(volatile uint32_t *)0x40049084) // Global Pin Control High Register
#define PORTA_ISFR		(*(volatile uint32_t *)0x400490A0) // Interrupt Status Flag Register
#define PORTB_PCR0		(*(volatile uint32_t *)0x4004A000) // Pin Control Register n
#define PORTB_PCR1		(*(volatile uint32_t *)0x4004A004) // Pin Control Register n
#define PORTB_PCR2		(*(volatile uint32_t *)0x4004A008) // Pin Control Register n
#define PORTB_PCR3		(*(volatile uint32_t *)0x4004A00C) // Pin Control Register n
#define PORTB_PCR4		(*(volatile uint32_t *)0x4004A010) // Pin Control Register n
#define PORTB_PCR5		(*(volatile uint32_t *)0x4004A014) // Pin Control Register n
#define PORTB_PCR6		(*(volatile uint32_t *)0x4004A018) // Pin Control Register n
#define PORTB_PCR7		(*(volatile uint32_t *)0x4004A01C) // Pin Control Register n
#define PORTB_PCR8		(*(volatile uint32_t *)0x4004A020) // Pin Control Register n
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
#define PORTD_PCR26		(*(volatile uint32_t *)0x4004C068) // Pin Control Register n
#define PORTD_PCR27		(*(volatile uint32_t *)0x4004C06C) // Pin Control Register n
#define PORTD_PCR28		(*(volatile uint32_t *)0x4004C070) // Pin Control Register n
#define PORTD_PCR29		(*(volatile uint32_t *)0x4004C074) // Pin Control Register n
#define PORTD_PCR30		(*(volatile uint32_t *)0x4004C078) // Pin Control Register n
#define PORTD_PCR31		(*(volatile uint32_t *)0x4004C07C) // Pin Control Register n
#define PORTD_GPCLR		(*(volatile uint32_t *)0x4004C080) // Global Pin Control Low Register
#define PORTD_GPCHR		(*(volatile uint32_t *)0x4004C084) // Global Pin Control High Register
#define PORTD_ISFR		(*(volatile uint32_t *)0x4004C0A0) // Interrupt Status Flag Register
#define PORTE_PCR0		(*(volatile uint32_t *)0x4004D000) // Pin Control Register n
#define PORTE_PCR1		(*(volatile uint32_t *)0x4004D004) // Pin Control Register n
#define PORTE_PCR2		(*(volatile uint32_t *)0x4004D008) // Pin Control Register n
#define PORTE_PCR3		(*(volatile uint32_t *)0x4004D00C) // Pin Control Register n
#define PORTE_PCR4		(*(volatile uint32_t *)0x4004D010) // Pin Control Register n
#define PORTE_PCR5		(*(volatile uint32_t *)0x4004D014) // Pin Control Register n
#define PORTE_PCR6		(*(volatile uint32_t *)0x4004D018) // Pin Control Register n
#define PORTE_PCR7		(*(volatile uint32_t *)0x4004D01C) // Pin Control Register n
#define PORTE_PCR8		(*(volatile uint32_t *)0x4004D020) // Pin Control Register n
#define PORTE_PCR9		(*(volatile uint32_t *)0x4004D024) // Pin Control Register n
#define PORTE_PCR10		(*(volatile uint32_t *)0x4004D028) // Pin Control Register n
#define PORTE_PCR11		(*(volatile uint32_t *)0x4004D02C) // Pin Control Register n
#define PORTE_PCR12		(*(volatile uint32_t *)0x4004D030) // Pin Control Register n
#define PORTE_PCR13		(*(volatile uint32_t *)0x4004D034) // Pin Control Register n
#define PORTE_PCR14		(*(volatile uint32_t *)0x4004D038) // Pin Control Register n
#define PORTE_PCR15		(*(volatile uint32_t *)0x4004D03C) // Pin Control Register n
#define PORTE_PCR16		(*(volatile uint32_t *)0x4004D040) // Pin Control Register n
#define PORTE_PCR17		(*(volatile uint32_t *)0x4004D044) // Pin Control Register n
#define PORTE_PCR18		(*(volatile uint32_t *)0x4004D048) // Pin Control Register n
#define PORTE_PCR19		(*(volatile uint32_t *)0x4004D04C) // Pin Control Register n
#define PORTE_PCR20		(*(volatile uint32_t *)0x4004D050) // Pin Control Register n
#define PORTE_PCR21		(*(volatile uint32_t *)0x4004D054) // Pin Control Register n
#define PORTE_PCR22		(*(volatile uint32_t *)0x4004D058) // Pin Control Register n
#define PORTE_PCR23		(*(volatile uint32_t *)0x4004D05C) // Pin Control Register n
#define PORTE_PCR24		(*(volatile uint32_t *)0x4004D060) // Pin Control Register n
#define PORTE_PCR25		(*(volatile uint32_t *)0x4004D064) // Pin Control Register n
#define PORTE_PCR26		(*(volatile uint32_t *)0x4004D068) // Pin Control Register n
#define PORTE_PCR27		(*(volatile uint32_t *)0x4004D06C) // Pin Control Register n
#define PORTE_PCR28		(*(volatile uint32_t *)0x4004D070) // Pin Control Register n
#define PORTE_PCR29		(*(volatile uint32_t *)0x4004D074) // Pin Control Register n
#define PORTE_PCR30		(*(volatile uint32_t *)0x4004D078) // Pin Control Register n
#define PORTE_PCR31		(*(volatile uint32_t *)0x4004D07C) // Pin Control Register n
#define PORTE_GPCLR		(*(volatile uint32_t *)0x4004D080) // Global Pin Control Low Register
#define PORTE_GPCHR		(*(volatile uint32_t *)0x4004D084) // Global Pin Control High Register
#define PORTE_ISFR		(*(volatile uint32_t *)0x4004D0A0) // Interrupt Status Flag Register

// Chapter 12: System Integration Module (SIM)
#define SIM_SOPT1		(*(volatile uint32_t *)0x40047000) // System Options Register 1
#define SIM_SOPT1CFG		(*(volatile uint32_t *)0x40047004) // SOPT1 Configuration Register
#define SIM_SOPT2		(*(volatile uint32_t *)0x40048004) // System Options Register 2
#define SIM_SOPT2_UART0SRC(n)           (uint32_t)(((n) & 3) << 26)     // UART0 Clock Source, 0=off, 1=FLL/PLL, 2=OSCERCLK, 3=MCGIRCLK
#define SIM_SOPT2_TPMSRC(n)             (uint32_t)(((n) & 3) << 24)     // TPM Clock Source, 0=off, 1=FLL/PLL, 2=OSCERCLK, 3=MCGIRCLK
#define SIM_SOPT2_USBSRC		((uint32_t)0x00040000)		// 0=USB_CLKIN, 1=FFL/PLL
#define SIM_SOPT2_PLLFLLSEL		((uint32_t)0x00010000)		// 0=FLL, 1=PLL
#define SIM_SOPT2_TRACECLKSEL		((uint32_t)0x00001000)		// 0=MCGOUTCLK, 1=CPU
#define SIM_SOPT2_PTD7PAD		((uint32_t)0x00000800)		// 0=normal, 1=double drive PTD7
#define SIM_SOPT2_CLKOUTSEL(n)		((uint32_t)(((n) & 7) << 5))	// Selects the clock to output on the CLKOUT pin.
#define SIM_SOPT2_RTCCLKOUTSEL		((uint32_t)0x00000010)		// RTC clock out select
#define SIM_SOPT4		(*(volatile uint32_t *)0x4004800C) // System Options Register 4
#define SIM_SOPT5		(*(volatile uint32_t *)0x40048010) // System Options Register 5
#define SIM_SOPT7		(*(volatile uint32_t *)0x40048018) // System Options Register 7
#define SIM_SDID		(*(const uint32_t *)0x40048024)    // System Device Identification Register
#define SIM_SCGC2		(*(volatile uint32_t *)0x4004802C) // System Clock Gating Control Register 2
#define SIM_SCGC2_DAC0			((uint32_t)0x00001000)		// DAC0 Clock Gate Control
#define SIM_SCGC3		(*(volatile uint32_t *)0x40048030) // System Clock Gating Control Register 3
#define SIM_SCGC3_ADC1			((uint32_t)0x08000000)		// ADC1 Clock Gate Control
#define SIM_SCGC3_FTM2			((uint32_t)0x01000000)		// FTM2 Clock Gate Control
#define SIM_SCGC4		(*(volatile uint32_t *)0x40048034) // System Clock Gating Control Register 4
#define SIM_SCGC4_VREF			((uint32_t)0x00100000)		// VREF Clock Gate Control
#define SIM_SCGC4_CMP			((uint32_t)0x00080000)		// Comparator Clock Gate Control
#define SIM_SCGC4_USBOTG		((uint32_t)0x00040000)		// USB Clock Gate Control
#define SIM_SCGC4_UART2			((uint32_t)0x00001000)		// UART2 Clock Gate Control
#define SIM_SCGC4_UART1			((uint32_t)0x00000800)		// UART1 Clock Gate Control
#define SIM_SCGC4_UART0			((uint32_t)0x00000400)		// UART0 Clock Gate Control
#define SIM_SCGC4_I2C1			((uint32_t)0x00000080)		// I2C1 Clock Gate Control
#define SIM_SCGC4_I2C0			((uint32_t)0x00000040)		// I2C0 Clock Gate Control
#define SIM_SCGC4_CMT			((uint32_t)0x00000004)		// CMT Clock Gate Control
#define SIM_SCGC4_EWM			((uint32_t)0x00000002)		// EWM Clock Gate Control
#ifdef KINETISL
#define SIM_SCGC4_SPI1			((uint32_t)0x00800000)		// 
#define SIM_SCGC4_SPI0			((uint32_t)0x00400000)		// 
#endif
#define SIM_SCGC5		(*(volatile uint32_t *)0x40048038) // System Clock Gating Control Register 5
#define SIM_SCGC5_PORTE			((uint32_t)0x00002000)		// Port E Clock Gate Control
#define SIM_SCGC5_PORTD			((uint32_t)0x00001000)		// Port D Clock Gate Control
#define SIM_SCGC5_PORTC			((uint32_t)0x00000800)		// Port C Clock Gate Control
#define SIM_SCGC5_PORTB			((uint32_t)0x00000400)		// Port B Clock Gate Control
#define SIM_SCGC5_PORTA			((uint32_t)0x00000200)		// Port A Clock Gate Control
#define SIM_SCGC5_TSI			((uint32_t)0x00000020)		// Touch Sense Input TSI Clock Gate Control
#define SIM_SCGC5_LPTIMER		((uint32_t)0x00000001)		// Low Power Timer Access Control
#define SIM_SCGC6		(*(volatile uint32_t *)0x4004803C) // System Clock Gating Control Register 6
#define SIM_SCGC6_DAC0			((uint32_t)0x80000000)		// DAC on Kinetis-L
#define SIM_SCGC6_RTC			((uint32_t)0x20000000)		// RTC Access
#define SIM_SCGC6_ADC0			((uint32_t)0x08000000)		// ADC0 Clock Gate Control
#define SIM_SCGC6_FTM1			((uint32_t)0x02000000)		// FTM1 Clock Gate Control
#define SIM_SCGC6_FTM0			((uint32_t)0x01000000)		// FTM0 Clock Gate Control
#define SIM_SCGC6_TPM2			((uint32_t)0x04000000)		// FTM1 Clock Gate Control
#define SIM_SCGC6_TPM1			((uint32_t)0x02000000)		// FTM1 Clock Gate Control
#define SIM_SCGC6_TPM0			((uint32_t)0x01000000)		// FTM0 Clock Gate Control
#define SIM_SCGC6_PIT			((uint32_t)0x00800000)		// PIT Clock Gate Control
#define SIM_SCGC6_PDB			((uint32_t)0x00400000)		// PDB Clock Gate Control
#define SIM_SCGC6_USBDCD		((uint32_t)0x00200000)		// USB DCD Clock Gate Control
#define SIM_SCGC6_CRC			((uint32_t)0x00040000)		// CRC Clock Gate Control
#define SIM_SCGC6_I2S			((uint32_t)0x00008000)		// I2S Clock Gate Control
#ifdef KINETISK
#define SIM_SCGC6_SPI1			((uint32_t)0x00002000)		// SPI1 Clock Gate Control
#define SIM_SCGC6_SPI0			((uint32_t)0x00001000)		// SPI0 Clock Gate Control
#endif
#define SIM_SCGC6_FLEXCAN0		((uint32_t)0x00000010)		// FlexCAN0 Clock Gate Control
#define SIM_SCGC6_DMAMUX		((uint32_t)0x00000002)		// DMA Mux Clock Gate Control
#define SIM_SCGC6_FTFL			((uint32_t)0x00000001)		// Flash Memory Clock Gate Control
#define SIM_SCGC7		(*(volatile uint32_t *)0x40048040) // System Clock Gating Control Register 7
#if defined(KINETISK)
#define SIM_SCGC7_DMA			((uint32_t)0x00000002)		// DMA Clock Gate Control
#elif defined(KINETISL)
#define SIM_SCGC7_DMA			((uint32_t)0x00000100)		// DMA Clock Gate Control
#endif
#define SIM_CLKDIV1		(*(volatile uint32_t *)0x40048044) // System Clock Divider Register 1
#define SIM_CLKDIV1_OUTDIV1(n)		((uint32_t)(((n) & 0x0F) << 28)) // divide value for the core/system clock
#define SIM_CLKDIV1_OUTDIV2(n)		((uint32_t)(((n) & 0x0F) << 24)) // divide value for the peripheral clock
#define SIM_CLKDIV1_OUTDIV3(n)		((uint32_t)(((n) & 0x0F) << 20)) // divide value for the flexbus clock
#define SIM_CLKDIV1_OUTDIV4(n)		((uint32_t)(((n) & 0x0F) << 16)) // divide value for the flash clock
#define SIM_CLKDIV2		(*(volatile uint32_t *)0x40048048) // System Clock Divider Register 2
#define SIM_CLKDIV2_USBDIV(n)		((uint32_t)(((n) & 0x07) << 1))
#define SIM_CLKDIV2_USBFRAC		((uint32_t)0x01)
#define SIM_FCFG1		(*(const uint32_t *)0x4004804C)    // Flash Configuration Register 1
#define SIM_FCFG2		(*(const uint32_t *)0x40048050)    // Flash Configuration Register 2
#define SIM_UIDH		(*(const uint32_t *)0x40048054)    // Unique Identification Register High
#define SIM_UIDMH		(*(const uint32_t *)0x40048058)    // Unique Identification Register Mid-High
#define SIM_UIDML		(*(const uint32_t *)0x4004805C)    // Unique Identification Register Mid Low
#define SIM_UIDL		(*(const uint32_t *)0x40048060)    // Unique Identification Register Low
#define SIM_COPC                (*(volatile uint32_t *)0x40048100) // COP Control Register (SIM_COPC)
#define SIM_SRVCOP              (*(volatile uint32_t *)0x40048104) // Service COP Register (SIM_SRVCOP)

// Chapter 13: Reset Control Module (RCM)
#define RCM_SRS0		(*(volatile uint8_t  *)0x4007F000) // System Reset Status Register 0
#define RCM_SRS0_POR			((uint8_t)0x80)
#define RCM_SRS0_PIN			((uint8_t)0x40)
#define RCM_SRS0_WDOG			((uint8_t)0x20)
#define RCM_SRS0_LOL			((uint8_t)0x08)
#define RCM_SRS0_LOC			((uint8_t)0x04)
#define RCM_SRS0_LVD			((uint8_t)0x02)
#define RCM_SRS0_WAKEUP			((uint8_t)0x01)
#define RCM_SRS1		(*(volatile uint8_t  *)0x4007F001) // System Reset Status Register 1
#define RCM_SRS1_SACKERR		((uint8_t)0x20)
#define RCM_SRS1_EZPT			((uint8_t)0x10)
#define RCM_SRS1_MDM_AP			((uint8_t)0x08)
#define RCM_SRS1_SW			((uint8_t)0x04)
#define RCM_SRS1_LOCKUP			((uint8_t)0x02)
#define RCM_SRS1_JTAG			((uint8_t)0x01)
#define RCM_RPFC		(*(volatile uint8_t  *)0x4007F004) // Reset Pin Filter Control Register
#define RCM_RPFW		(*(volatile uint8_t  *)0x4007F005) // Reset Pin Filter Width Register
#define RCM_MR			(*(volatile uint8_t  *)0x4007F007) // Mode Register

// Chapter 14: System Mode Controller
#define SMC_PMPROT		(*(volatile uint8_t  *)0x4007E000) // Power Mode Protection Register
#define SMC_PMPROT_AVLP			((uint8_t)0x20)			// Allow very low power modes
#define SMC_PMPROT_ALLS			((uint8_t)0x08)			// Allow low leakage stop mode
#define SMC_PMPROT_AVLLS		((uint8_t)0x02)			// Allow very low leakage stop mode
#define SMC_PMCTRL		(*(volatile uint8_t  *)0x4007E001) // Power Mode Control Register
#define SMC_PMCTRL_LPWUI		((uint8_t)0x80)			// Low Power Wake Up on Interrupt
#define SMC_PMCTRL_RUNM(n)		((uint8_t)(((n) & 0x03) << 5))	// Run Mode Control
#define SMC_PMCTRL_STOPA		((uint8_t)0x08)			// Stop Aborted
#define SMC_PMCTRL_STOPM(n)		((uint8_t)((n) & 0x07))		// Stop Mode Control
#define SMC_VLLSCTRL		(*(volatile uint8_t  *)0x4007E002) // VLLS Control Register
#define SMC_VLLSCTRL_PORPO		((uint8_t)0x20)			// POR Power Option
#define SMC_VLLSCTRL_VLLSM(n)		((uint8_t)((n) & 0x07))		// VLLS Mode Control
#define SMC_PMSTAT		(*(volatile uint8_t  *)0x4007E003) // Power Mode Status Register
#define SMC_PMSTAT_RUN			((uint8_t)0x01)			// Current power mode is RUN
#define SMC_PMSTAT_STOP			((uint8_t)0x02)			// Current power mode is STOP
#define SMC_PMSTAT_VLPR			((uint8_t)0x04)			// Current power mode is VLPR
#define SMC_PMSTAT_VLPW			((uint8_t)0x08)			// Current power mode is VLPW
#define SMC_PMSTAT_VLPS			((uint8_t)0x10)			// Current power mode is VLPS
#define SMC_PMSTAT_LLS			((uint8_t)0x20)			// Current power mode is LLS
#define SMC_PMSTAT_VLLS			((uint8_t)0x40)			// Current power mode is VLLS

// Chapter 15: Power Management Controller
#define PMC_LVDSC1		(*(volatile uint8_t  *)0x4007D000) // Low Voltage Detect Status And Control 1 register
#define PMC_LVDSC1_LVDF			((uint8_t)0x80)			// Low-Voltage Detect Flag
#define PMC_LVDSC1_LVDACK		((uint8_t)0x40)			// Low-Voltage Detect Acknowledge
#define PMC_LVDSC1_LVDIE		((uint8_t)0x20)			// Low-Voltage Detect Interrupt Enable
#define PMC_LVDSC1_LVDRE		((uint8_t)0x10)			// Low-Voltage Detect Reset Enable
#define PMC_LVDSC1_LVDV(n)		((uint8_t)((n) & 0x03))		// Low-Voltage Detect Voltage Select
#define PMC_LVDSC2		(*(volatile uint8_t  *)0x4007D001) // Low Voltage Detect Status And Control 2 register
#define PMC_LVDSC2_LVWF			((uint8_t)0x80)			// Low-Voltage Warning Flag
#define PMC_LVDSC2_LVWACK		((uint8_t)0x40)			// Low-Voltage Warning Acknowledge
#define PMC_LVDSC2_LVWIE		((uint8_t)0x20)			// Low-Voltage Warning Interrupt Enable
#define PMC_LVDSC2_LVWV(n)		((uint8_t)((n) & 0x03))		// Low-Voltage Warning Voltage Select
#define PMC_REGSC		(*(volatile uint8_t  *)0x4007D002) // Regulator Status And Control register
#define PMC_REGSC_BGEN			((uint8_t)0x10)			// Bandgap Enable In VLPx Operation
#define PMC_REGSC_ACKISO		((uint8_t)0x08)			// Acknowledge Isolation
#define PMC_REGSC_REGONS		((uint8_t)0x04)			// Regulator In Run Regulation Status
#define PMC_REGSC_BGBE			((uint8_t)0x01)			// Bandgap Buffer Enable

// Chapter 16: Low-Leakage Wakeup Unit (LLWU)
#define LLWU_PE1		(*(volatile uint8_t  *)0x4007C000) // LLWU Pin Enable 1 register
#define LLWU_PE2		(*(volatile uint8_t  *)0x4007C001) // LLWU Pin Enable 2 register
#define LLWU_PE3		(*(volatile uint8_t  *)0x4007C002) // LLWU Pin Enable 3 register
#define LLWU_PE4		(*(volatile uint8_t  *)0x4007C003) // LLWU Pin Enable 4 register
#define LLWU_ME			(*(volatile uint8_t  *)0x4007C004) // LLWU Module Enable register
#define LLWU_F1			(*(volatile uint8_t  *)0x4007C005) // LLWU Flag 1 register
#define LLWU_F2			(*(volatile uint8_t  *)0x4007C006) // LLWU Flag 2 register
#define LLWU_F3			(*(volatile uint8_t  *)0x4007C007) // LLWU Flag 3 register
#define LLWU_FILT1		(*(volatile uint8_t  *)0x4007C008) // LLWU Pin Filter 1 register
#define LLWU_FILT2		(*(volatile uint8_t  *)0x4007C009) // LLWU Pin Filter 2 register
#define LLWU_RST		(*(volatile uint8_t  *)0x4007C00A) // LLWU Reset Enable register

// Chapter 17: Miscellaneous Control Module (MCM)
#if defined(KINETISK)
#define MCM_PLASC		(*(volatile uint16_t *)0xE0080008) // Crossbar Switch (AXBS) Slave Configuration
#define MCM_PLAMC		(*(volatile uint16_t *)0xE008000A) // Crossbar Switch (AXBS) Master Configuration
#define MCM_PLACR		(*(volatile uint32_t *)0xE008000C) // Crossbar Switch (AXBS) Control Register (MK20DX128)
#define MCM_PLACR_ARG			((uint32_t)0x00000200)		// Arbitration select, 0=fixed, 1=round-robin
#define MCM_CR			(*(volatile uint32_t *)0xE008000C) // RAM arbitration control register (MK20DX256)
#define MCM_CR_SRAMLWP			((uint32_t)0x40000000)		// SRAM_L write protect
#define MCM_CR_SRAMLAP(n)		((uint32_t)(((n) & 0x03) << 28)) // SRAM_L priority, 0=RR, 1=favor DMA, 2=CPU, 3=DMA
#define MCM_CR_SRAMUWP			((uint32_t)0x04000000)		// SRAM_U write protect
#define MCM_CR_SRAMUAP(n)		((uint32_t)(((n) & 0x03) << 24)) // SRAM_U priority, 0=RR, 1=favor DMA, 2=CPU, 3=DMA
#elif defined(KINETISL)
#define MCM_PLASC               (*(volatile uint16_t *)0xF0003008) // Crossbar Switch (AXBS) Slave Configuration
#define MCM_PLAMC               (*(volatile uint16_t *)0xF000300A) // Crossbar Switch (AXBS) Master Configuration
#define MCM_PLACR               (*(volatile uint32_t *)0xF000300C) // Platform Control Register
#define MCM_PLACR_ESFC			((uint32_t)0x00010000)		// Enable Stalling Flash Controller
#define MCM_PLACR_DFCS			((uint32_t)0x00008000)		// Disable Flash Controller Speculation
#define MCM_PLACR_EFDS			((uint32_t)0x00004000)		// Enable Flash Data Speculation
#define MCM_PLACR_DFCC			((uint32_t)0x00002000)		// Disable Flash Controller Cache
#define MCM_PLACR_DFCIC			((uint32_t)0x00001000)		// Disable Flash Controller Instruction Caching
#define MCM_PLACR_DFCDA			((uint32_t)0x00000800)		// Disable Flash Controller Data Caching
#define MCM_PLACR_CFCC			((uint32_t)0x00000400)		// Clear Flash Controller Cache
#define MCM_PLACR_ARB			((uint32_t)0x00000200)		// Arbitration select
#define MCM_CPO                 (*(volatile uint32_t *)0xF0003040) // Compute Operation Control Register
#endif

// Crossbar Switch (AXBS) - only programmable on MK20DX256
#define AXBS_PRS0		(*(volatile uint32_t *)0x40004000) // Priority Registers Slave 0
#define AXBS_CRS0		(*(volatile uint32_t *)0x40004010) // Control Register 0
#define AXBS_PRS1		(*(volatile uint32_t *)0x40004100) // Priority Registers Slave 1
#define AXBS_CRS1		(*(volatile uint32_t *)0x40004110) // Control Register 1
#define AXBS_PRS2		(*(volatile uint32_t *)0x40004200) // Priority Registers Slave 2
#define AXBS_CRS2		(*(volatile uint32_t *)0x40004210) // Control Register 2
#define AXBS_PRS3		(*(volatile uint32_t *)0x40004300) // Priority Registers Slave 3
#define AXBS_CRS3		(*(volatile uint32_t *)0x40004310) // Control Register 3
#define AXBS_PRS4		(*(volatile uint32_t *)0x40004400) // Priority Registers Slave 4
#define AXBS_CRS4		(*(volatile uint32_t *)0x40004410) // Control Register 4
#define AXBS_PRS5		(*(volatile uint32_t *)0x40004500) // Priority Registers Slave 5
#define AXBS_CRS5		(*(volatile uint32_t *)0x40004510) // Control Register 5
#define AXBS_PRS6		(*(volatile uint32_t *)0x40004600) // Priority Registers Slave 6
#define AXBS_CRS6		(*(volatile uint32_t *)0x40004610) // Control Register 6
#define AXBS_PRS7		(*(volatile uint32_t *)0x40004700) // Priority Registers Slave 7
#define AXBS_CRS7		(*(volatile uint32_t *)0x40004710) // Control Register 7
#define AXBS_MGPCR0		(*(volatile uint32_t *)0x40004800) // Master 0 General Purpose Control Register
#define AXBS_MGPCR1		(*(volatile uint32_t *)0x40004900) // Master 1 General Purpose Control Register
#define AXBS_MGPCR2		(*(volatile uint32_t *)0x40004A00) // Master 2 General Purpose Control Register
#define AXBS_MGPCR3		(*(volatile uint32_t *)0x40004B00) // Master 3 General Purpose Control Register
#define AXBS_MGPCR4		(*(volatile uint32_t *)0x40004C00) // Master 4 General Purpose Control Register
#define AXBS_MGPCR5		(*(volatile uint32_t *)0x40004D00) // Master 5 General Purpose Control Register
#define AXBS_MGPCR6		(*(volatile uint32_t *)0x40004E00) // Master 6 General Purpose Control Register
#define AXBS_MGPCR7		(*(volatile uint32_t *)0x40004F00) // Master 7 General Purpose Control Register
#define AXBS_CRS_READONLY		((uint32_t)0x80000000)
#define AXBS_CRS_HALTLOWPRIORITY	((uint32_t)0x40000000)
#define AXBS_CRS_ARB_FIXED		((uint32_t)0x00000000)
#define AXBS_CRS_ARB_ROUNDROBIN		((uint32_t)0x00010000)
#define AXBS_CRS_PARK_FIXED		((uint32_t)0x00000000)
#define AXBS_CRS_PARK_PREVIOUS		((uint32_t)0x00000010)
#define AXBS_CRS_PARK_NONE		((uint32_t)0x00000020)
#define AXBS_CRS_PARK(n)		((uint32_t)(((n) & 7) << 0))



// Chapter 20: Direct Memory Access Multiplexer (DMAMUX)
#define DMAMUX0_CHCFG0		(*(volatile uint8_t  *)0x40021000) // Channel Configuration register
#define DMAMUX0_CHCFG1		(*(volatile uint8_t  *)0x40021001) // Channel Configuration register
#define DMAMUX0_CHCFG2		(*(volatile uint8_t  *)0x40021002) // Channel Configuration register
#define DMAMUX0_CHCFG3		(*(volatile uint8_t  *)0x40021003) // Channel Configuration register
#define DMAMUX0_CHCFG4		(*(volatile uint8_t  *)0x40021004) // Channel Configuration register
#define DMAMUX0_CHCFG5		(*(volatile uint8_t  *)0x40021005) // Channel Configuration register
#define DMAMUX0_CHCFG6		(*(volatile uint8_t  *)0x40021006) // Channel Configuration register
#define DMAMUX0_CHCFG7		(*(volatile uint8_t  *)0x40021007) // Channel Configuration register
#define DMAMUX0_CHCFG8		(*(volatile uint8_t  *)0x40021008) // Channel Configuration register
#define DMAMUX0_CHCFG9		(*(volatile uint8_t  *)0x40021009) // Channel Configuration register
#define DMAMUX0_CHCFG10		(*(volatile uint8_t  *)0x4002100A) // Channel Configuration register
#define DMAMUX0_CHCFG11		(*(volatile uint8_t  *)0x4002100B) // Channel Configuration register
#define DMAMUX0_CHCFG12		(*(volatile uint8_t  *)0x4002100C) // Channel Configuration register
#define DMAMUX0_CHCFG13		(*(volatile uint8_t  *)0x4002100D) // Channel Configuration register
#define DMAMUX0_CHCFG14		(*(volatile uint8_t  *)0x4002100E) // Channel Configuration register
#define DMAMUX0_CHCFG15		(*(volatile uint8_t  *)0x4002100F) // Channel Configuration register
#define DMAMUX_DISABLE			0
#define DMAMUX_TRIG			64
#define DMAMUX_ENABLE			128
#define DMAMUX_SOURCE_UART0_RX		2
#define DMAMUX_SOURCE_UART0_TX		3
#define DMAMUX_SOURCE_UART1_RX		4
#define DMAMUX_SOURCE_UART1_TX		5
#define DMAMUX_SOURCE_UART2_RX		6
#define DMAMUX_SOURCE_UART2_TX		7
#define DMAMUX_SOURCE_I2S0_RX		14
#define DMAMUX_SOURCE_I2S0_TX		15
#define DMAMUX_SOURCE_SPI0_RX		16
#define DMAMUX_SOURCE_SPI0_TX		17
#define DMAMUX_SOURCE_SPI1_RX		18
#define DMAMUX_SOURCE_SPI1_TX		19
#define DMAMUX_SOURCE_I2C0		22
#define DMAMUX_SOURCE_I2C1		23
#define DMAMUX_SOURCE_FTM0_CH0		24
#define DMAMUX_SOURCE_FTM0_CH1		25
#define DMAMUX_SOURCE_FTM0_CH2		26
#define DMAMUX_SOURCE_FTM0_CH3		27
#define DMAMUX_SOURCE_FTM0_CH4		28
#define DMAMUX_SOURCE_FTM0_CH5		29
#define DMAMUX_SOURCE_FTM0_CH6		30
#define DMAMUX_SOURCE_FTM0_CH7		31
#define DMAMUX_SOURCE_FTM1_CH0		32
#define DMAMUX_SOURCE_FTM1_CH1		33
#define DMAMUX_SOURCE_FTM2_CH0		34
#define DMAMUX_SOURCE_FTM2_CH1		35
#define DMAMUX_SOURCE_ADC0		40
#define DMAMUX_SOURCE_ADC1		41
#define DMAMUX_SOURCE_CMP0		42
#define DMAMUX_SOURCE_CMP1		43
#define DMAMUX_SOURCE_CMP2		44
#define DMAMUX_SOURCE_DAC0		45
#define DMAMUX_SOURCE_CMT		47
#define DMAMUX_SOURCE_PDB		48
#define DMAMUX_SOURCE_PORTA		49
#define DMAMUX_SOURCE_PORTB		50
#define DMAMUX_SOURCE_PORTC		51
#define DMAMUX_SOURCE_PORTD		52
#define DMAMUX_SOURCE_PORTE		53
#if defined(KINETISK)
#define DMAMUX_SOURCE_ALWAYS0		54
#define DMAMUX_SOURCE_ALWAYS1		55
#define DMAMUX_SOURCE_ALWAYS2		56
#define DMAMUX_SOURCE_ALWAYS3		57
#define DMAMUX_SOURCE_ALWAYS4		58
#define DMAMUX_SOURCE_ALWAYS5		59
#define DMAMUX_SOURCE_ALWAYS6		60
#define DMAMUX_SOURCE_ALWAYS7		61
#define DMAMUX_SOURCE_ALWAYS8		62
#define DMAMUX_SOURCE_ALWAYS9		63
#define DMAMUX_NUM_SOURCE_ALWAYS	10
#elif defined(KINETISL)
#define DMAMUX_SOURCE_FTM0_OV		54
#define DMAMUX_SOURCE_FTM1_OV		55
#define DMAMUX_SOURCE_FTM2_OV		56
#define DMAMUX_SOURCE_TSI		57
#define DMAMUX_SOURCE_ALWAYS0		60
#define DMAMUX_SOURCE_ALWAYS1		61
#define DMAMUX_SOURCE_ALWAYS2		62
#define DMAMUX_SOURCE_ALWAYS3		63
#define DMAMUX_NUM_SOURCE_ALWAYS	4
#endif

// Chapter 21: Direct Memory Access Controller (eDMA)
#if defined(KINETISK)
#define DMA_CR			(*(volatile uint32_t *)0x40008000) // Control Register
#define DMA_CR_CX			((uint32_t)(1<<17))	// Cancel Transfer
#define DMA_CR_ECX			((uint32_t)(1<<16))	// Error Cancel Transfer
#define DMA_CR_EMLM			((uint32_t)0x80)	// Enable Minor Loop Mapping
#define DMA_CR_CLM			((uint32_t)0x40)	// Continuous Link Mode
#define DMA_CR_HALT			((uint32_t)0x20)	// Halt DMA Operations
#define DMA_CR_HOE			((uint32_t)0x10)	// Halt On Error
#define DMA_CR_ERCA			((uint32_t)0x04)	// Enable Round Robin Channel Arbitration
#define DMA_CR_EDBG			((uint32_t)0x02)	// Enable Debug
#define DMA_ES			(*(volatile uint32_t *)0x40008004) // Error Status Register
#define DMA_ERQ			(*(volatile uint32_t *)0x4000800C) // Enable Request Register
#define DMA_ERQ_ERQ0			((uint32_t)1<<0)	// Enable DMA Request 0
#define DMA_ERQ_ERQ1			((uint32_t)1<<1)	// Enable DMA Request 1
#define DMA_ERQ_ERQ2			((uint32_t)1<<2)	// Enable DMA Request 2
#define DMA_ERQ_ERQ3			((uint32_t)1<<3)	// Enable DMA Request 3
#define DMA_ERQ_ERQ4			((uint32_t)1<<4)	// Enable DMA Request 4
#define DMA_ERQ_ERQ5			((uint32_t)1<<5)	// Enable DMA Request 5
#define DMA_ERQ_ERQ6			((uint32_t)1<<6)	// Enable DMA Request 6
#define DMA_ERQ_ERQ7			((uint32_t)1<<7)	// Enable DMA Request 7
#define DMA_ERQ_ERQ8			((uint32_t)1<<8)	// Enable DMA Request 8
#define DMA_ERQ_ERQ9			((uint32_t)1<<9)	// Enable DMA Request 9
#define DMA_ERQ_ERQ10			((uint32_t)1<<10)	// Enable DMA Request 10
#define DMA_ERQ_ERQ11			((uint32_t)1<<11)	// Enable DMA Request 11
#define DMA_ERQ_ERQ12			((uint32_t)1<<12)	// Enable DMA Request 12
#define DMA_ERQ_ERQ13			((uint32_t)1<<13)	// Enable DMA Request 13
#define DMA_ERQ_ERQ14			((uint32_t)1<<14)	// Enable DMA Request 14
#define DMA_ERQ_ERQ15			((uint32_t)1<<15)	// Enable DMA Request 15
#define DMA_EEI			(*(volatile uint32_t *)0x40008014) // Enable Error Interrupt Register
#define DMA_EEI_EEI0			((uint32_t)1<<0)	// Enable Error Interrupt 0
#define DMA_EEI_EEI1			((uint32_t)1<<1)	// Enable Error Interrupt 1
#define DMA_EEI_EEI2			((uint32_t)1<<2)	// Enable Error Interrupt 2
#define DMA_EEI_EEI3			((uint32_t)1<<3)	// Enable Error Interrupt 3
#define DMA_EEI_EEI4			((uint32_t)1<<4)	// Enable Error Interrupt 4
#define DMA_EEI_EEI5			((uint32_t)1<<5)	// Enable Error Interrupt 5
#define DMA_EEI_EEI6			((uint32_t)1<<6)	// Enable Error Interrupt 6
#define DMA_EEI_EEI7			((uint32_t)1<<7)	// Enable Error Interrupt 7
#define DMA_EEI_EEI8			((uint32_t)1<<8)	// Enable Error Interrupt 8
#define DMA_EEI_EEI9			((uint32_t)1<<9)	// Enable Error Interrupt 9
#define DMA_EEI_EEI10			((uint32_t)1<<10)	// Enable Error Interrupt 10
#define DMA_EEI_EEI11			((uint32_t)1<<11)	// Enable Error Interrupt 11
#define DMA_EEI_EEI12			((uint32_t)1<<12)	// Enable Error Interrupt 12
#define DMA_EEI_EEI13			((uint32_t)1<<13)	// Enable Error Interrupt 13
#define DMA_EEI_EEI14			((uint32_t)1<<14)	// Enable Error Interrupt 14
#define DMA_EEI_EEI15			((uint32_t)1<<15)	// Enable Error Interrupt 15
#define DMA_CEEI		(*(volatile uint8_t  *)0x40008018) // Clear Enable Error Interrupt Register
#define DMA_CEEI_CEEI(n)		((uint8_t)(n & 15)<<0)	// Clear Enable Error Interrupt
#define DMA_CEEI_CAEE			((uint8_t)1<<6)		// Clear All Enable Error Interrupts
#define DMA_CEEI_NOP			((uint8_t)1<<7)		// NOP
#define DMA_SEEI		(*(volatile uint8_t  *)0x40008019) // Set Enable Error Interrupt Register
#define DMA_SEEI_SEEI(n)		((uint8_t)(n & 15)<<0)	// Set Enable Error Interrupt
#define DMA_SEEI_SAEE			((uint8_t)1<<6)		// Set All Enable Error Interrupts
#define DMA_SEEI_NOP			((uint8_t)1<<7)		// NOP
#define DMA_CERQ		(*(volatile uint8_t  *)0x4000801A) // Clear Enable Request Register
#define DMA_CERQ_CERQ(n)		((uint8_t)(n & 15)<<0)	// Clear Enable Request
#define DMA_CERQ_CAER			((uint8_t)1<<6)		// Clear All Enable Requests
#define DMA_CERQ_NOP			((uint8_t)1<<7)		// NOP
#define DMA_SERQ		(*(volatile uint8_t  *)0x4000801B) // Set Enable Request Register
#define DMA_SERQ_SERQ(n)		((uint8_t)(n & 15)<<0)	// Set Enable Request
#define DMA_SERQ_SAER			((uint8_t)1<<6)		// Set All Enable Requests
#define DMA_SERQ_NOP			((uint8_t)1<<7)		// NOP
#define DMA_CDNE		(*(volatile uint8_t  *)0x4000801C) // Clear DONE Status Bit Register
#define DMA_CDNE_CDNE(n)		((uint8_t)(n & 15)<<0)	// Clear Done Bit
#define DMA_CDNE_CADN			((uint8_t)1<<6)		// Clear All Done Bits
#define DMA_CDNE_NOP			((uint8_t)1<<7)		// NOP
#define DMA_SSRT		(*(volatile uint8_t  *)0x4000801D) // Set START Bit Register
#define DMA_SSRT_SSRT(n)		((uint8_t)(n & 15)<<0)	// Set Start Bit
#define DMA_SSRT_SAST			((uint8_t)1<<6)		// Set All Start Bits
#define DMA_SSRT_NOP			((uint8_t)1<<7)		// NOP
#define DMA_CERR		(*(volatile uint8_t  *)0x4000801E) // Clear Error Register
#define DMA_CERR_CERR(n)		((uint8_t)(n & 15)<<0)	// Clear Error Indicator
#define DMA_CERR_CAEI			((uint8_t)1<<6)		// Clear All Error Indicators
#define DMA_CERR_NOP			((uint8_t)1<<7)		// NOP
#define DMA_CINT		(*(volatile uint8_t  *)0x4000801F) // Clear Interrupt Request Register
#define DMA_CINT_CINT(n)		((uint8_t)(n & 15)<<0)	// Clear Interrupt Request
#define DMA_CINT_CAIR			((uint8_t)1<<6)		// Clear All Interrupt Requests
#define DMA_CINT_NOP			((uint8_t)1<<7)		// NOP
#define DMA_INT			(*(volatile uint32_t *)0x40008024) // Interrupt Request Register
#define DMA_INT_INT0			((uint32_t)1<<0)	// Interrupt Request 0
#define DMA_INT_INT1			((uint32_t)1<<1)	// Interrupt Request 1
#define DMA_INT_INT2			((uint32_t)1<<2)	// Interrupt Request 2
#define DMA_INT_INT3			((uint32_t)1<<3)	// Interrupt Request 3
#define DMA_INT_INT4			((uint32_t)1<<4)	// Interrupt Request 4
#define DMA_INT_INT5			((uint32_t)1<<5)	// Interrupt Request 5
#define DMA_INT_INT6			((uint32_t)1<<6)	// Interrupt Request 6
#define DMA_INT_INT7			((uint32_t)1<<7)	// Interrupt Request 7
#define DMA_INT_INT8			((uint32_t)1<<8)	// Interrupt Request 8
#define DMA_INT_INT9			((uint32_t)1<<9)	// Interrupt Request 9
#define DMA_INT_INT10			((uint32_t)1<<10)	// Interrupt Request 10
#define DMA_INT_INT11			((uint32_t)1<<11)	// Interrupt Request 11
#define DMA_INT_INT12			((uint32_t)1<<12)	// Interrupt Request 12
#define DMA_INT_INT13			((uint32_t)1<<13)	// Interrupt Request 13
#define DMA_INT_INT14			((uint32_t)1<<14)	// Interrupt Request 14
#define DMA_INT_INT15			((uint32_t)1<<15)	// Interrupt Request 15
#define DMA_ERR			(*(volatile uint32_t *)0x4000802C) // Error Register
#define DMA_ERR_ERR0			((uint32_t)1<<0)	// Error in Channel 0
#define DMA_ERR_ERR1			((uint32_t)1<<1)	// Error in Channel 1
#define DMA_ERR_ERR2			((uint32_t)1<<2)	// Error in Channel 2
#define DMA_ERR_ERR3			((uint32_t)1<<3)	// Error in Channel 3
#define DMA_ERR_ERR4			((uint32_t)1<<4)	// Error in Channel 4
#define DMA_ERR_ERR5			((uint32_t)1<<5)	// Error in Channel 5
#define DMA_ERR_ERR6			((uint32_t)1<<6)	// Error in Channel 6
#define DMA_ERR_ERR7			((uint32_t)1<<7)	// Error in Channel 7
#define DMA_ERR_ERR8			((uint32_t)1<<8)	// Error in Channel 8
#define DMA_ERR_ERR9			((uint32_t)1<<9)	// Error in Channel 9
#define DMA_ERR_ERR10			((uint32_t)1<<10)	// Error in Channel 10
#define DMA_ERR_ERR11			((uint32_t)1<<11)	// Error in Channel 11
#define DMA_ERR_ERR12			((uint32_t)1<<12)	// Error in Channel 12
#define DMA_ERR_ERR13			((uint32_t)1<<13)	// Error in Channel 13
#define DMA_ERR_ERR14			((uint32_t)1<<14)	// Error in Channel 14
#define DMA_ERR_ERR15			((uint32_t)1<<15)	// Error in Channel 15
#define DMA_HRS			(*(volatile uint32_t *)0x40008034) // Hardware Request Status Register
#define DMA_HRS_HRS0			((uint32_t)1<<0)	// Hardware Request Status Channel 0
#define DMA_HRS_HRS1			((uint32_t)1<<1)	// Hardware Request Status Channel 1
#define DMA_HRS_HRS2			((uint32_t)1<<2)	// Hardware Request Status Channel 2
#define DMA_HRS_HRS3			((uint32_t)1<<3)	// Hardware Request Status Channel 3
#define DMA_HRS_HRS4			((uint32_t)1<<4)	// Hardware Request Status Channel 4
#define DMA_HRS_HRS5			((uint32_t)1<<5)	// Hardware Request Status Channel 5
#define DMA_HRS_HRS6			((uint32_t)1<<6)	// Hardware Request Status Channel 6
#define DMA_HRS_HRS7			((uint32_t)1<<7)	// Hardware Request Status Channel 7
#define DMA_HRS_HRS8			((uint32_t)1<<8)	// Hardware Request Status Channel 8
#define DMA_HRS_HRS9			((uint32_t)1<<9)	// Hardware Request Status Channel 9
#define DMA_HRS_HRS10			((uint32_t)1<<10)	// Hardware Request Status Channel 10
#define DMA_HRS_HRS11			((uint32_t)1<<11)	// Hardware Request Status Channel 11
#define DMA_HRS_HRS12			((uint32_t)1<<12)	// Hardware Request Status Channel 12
#define DMA_HRS_HRS13			((uint32_t)1<<13)	// Hardware Request Status Channel 13
#define DMA_HRS_HRS14			((uint32_t)1<<14)	// Hardware Request Status Channel 14
#define DMA_HRS_HRS15			((uint32_t)1<<15)	// Hardware Request Status Channel 15
#define DMA_DCHPRI3		(*(volatile uint8_t  *)0x40008100) // Channel n Priority Register
#define DMA_DCHPRI2		(*(volatile uint8_t  *)0x40008101) // Channel n Priority Register
#define DMA_DCHPRI1		(*(volatile uint8_t  *)0x40008102) // Channel n Priority Register
#define DMA_DCHPRI0		(*(volatile uint8_t  *)0x40008103) // Channel n Priority Register
#define DMA_DCHPRI_CHPRI(n)		((uint8_t)(n & 15)<<0)	// Channel Arbitration Priority
#define DMA_DCHPRI_DPA			((uint8_t)1<<6)		// Disable PreEmpt Ability
#define DMA_DCHPRI_ECP			((uint8_t)1<<7)		// Enable PreEmption
#define DMA_DCHPRI7		(*(volatile uint8_t  *)0x40008104) // Channel n Priority Register
#define DMA_DCHPRI6		(*(volatile uint8_t  *)0x40008105) // Channel n Priority Register
#define DMA_DCHPRI5		(*(volatile uint8_t  *)0x40008106) // Channel n Priority Register
#define DMA_DCHPRI4		(*(volatile uint8_t  *)0x40008107) // Channel n Priority Register
#define DMA_DCHPRI11		(*(volatile uint8_t  *)0x40008108) // Channel n Priority Register
#define DMA_DCHPRI10		(*(volatile uint8_t  *)0x40008109) // Channel n Priority Register
#define DMA_DCHPRI9		(*(volatile uint8_t  *)0x4000810A) // Channel n Priority Register
#define DMA_DCHPRI8		(*(volatile uint8_t  *)0x4000810B) // Channel n Priority Register
#define DMA_DCHPRI15		(*(volatile uint8_t  *)0x4000810C) // Channel n Priority Register
#define DMA_DCHPRI14		(*(volatile uint8_t  *)0x4000810D) // Channel n Priority Register
#define DMA_DCHPRI13		(*(volatile uint8_t  *)0x4000810E) // Channel n Priority Register
#define DMA_DCHPRI12		(*(volatile uint8_t  *)0x4000810F) // Channel n Priority Register
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
